iryek-rpi/pico-encoder/hw/case/case.jpg

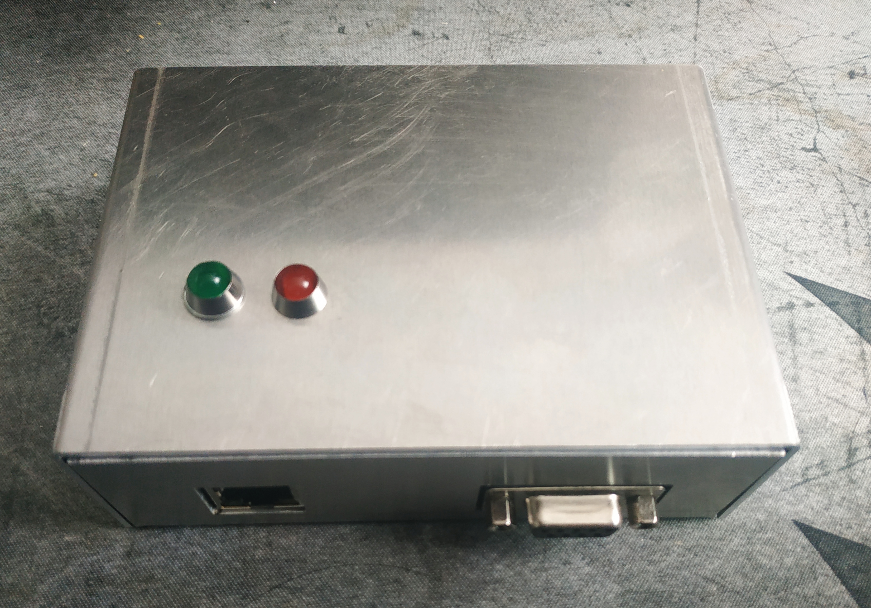
hw/case/case.jpg
