iryek-rpi/pico-encoder/hw/case/silk/chuja-si.jpg

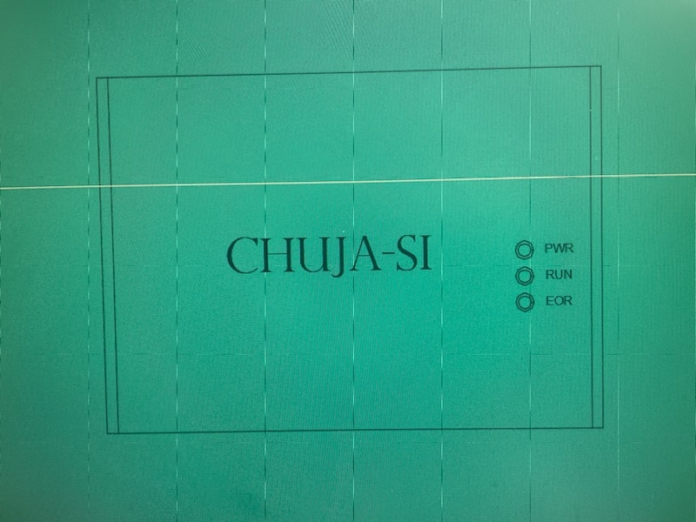
hw/case/silk/chuja-si.jpg
