iryek-rpi/pico-encoder/hw/case/silk/front-back.jpg

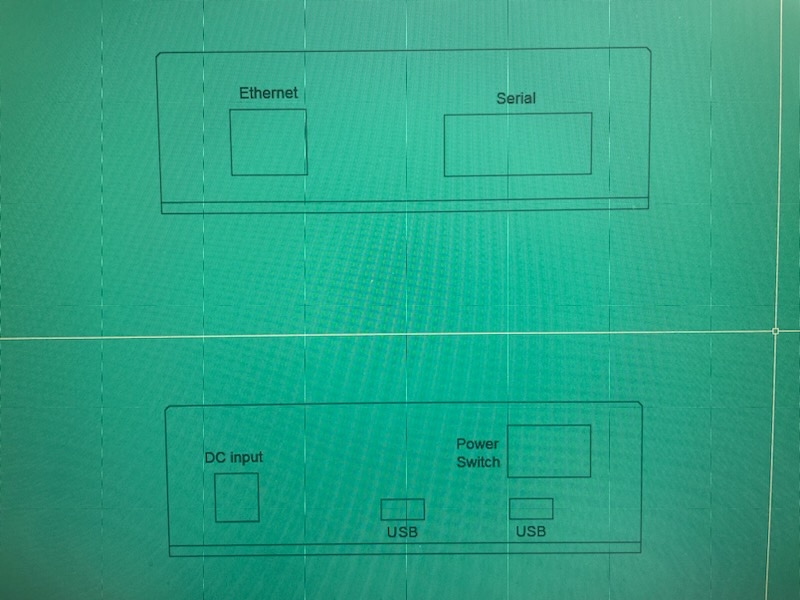
hw/case/silk/front-back.jpg
