iryek-rpi/pico-encoder/hw/share/connected0.png

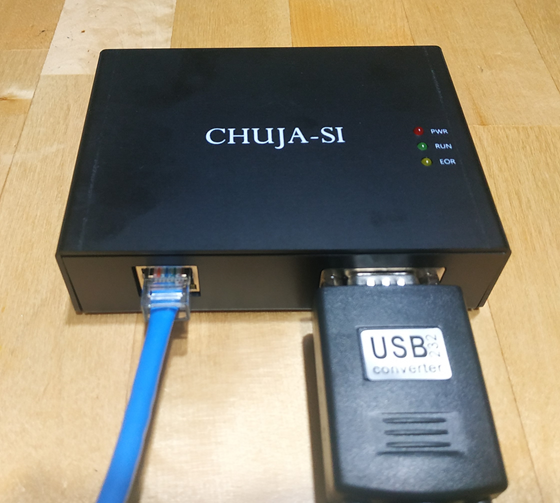
hw/share/connected0.png
