iryek-rpi/pico-encoder/kc/w5500-evb-pico-pcb.png

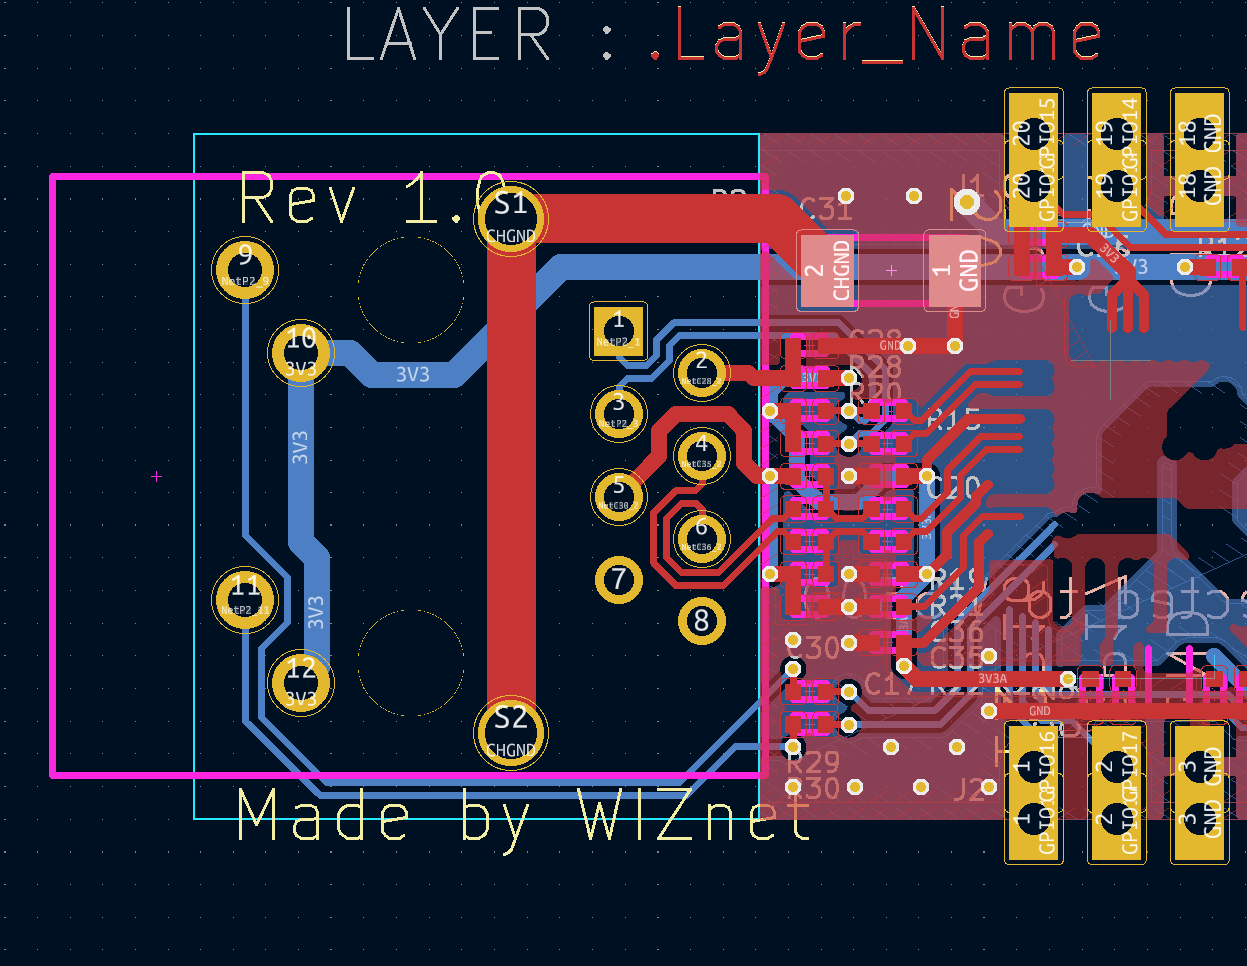
kc/w5500-evb-pico-pcb.png
