iryek-rpi/pico-encoder/kc/w5500-evb-pico-sch.png

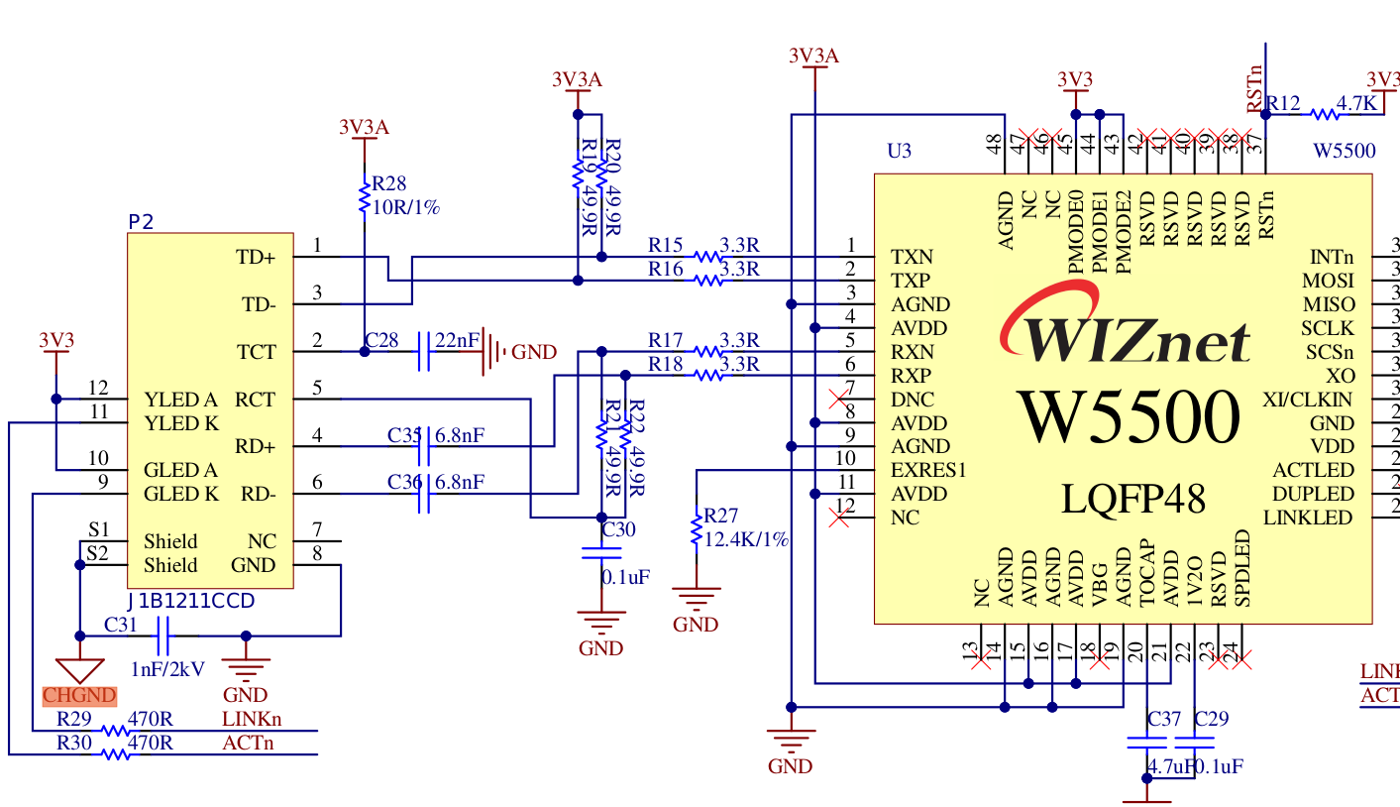
kc/w5500-evb-pico-sch.png
