iryek-rpi/pico-encoder/kc/w5500-rvb-pico-board.jpg

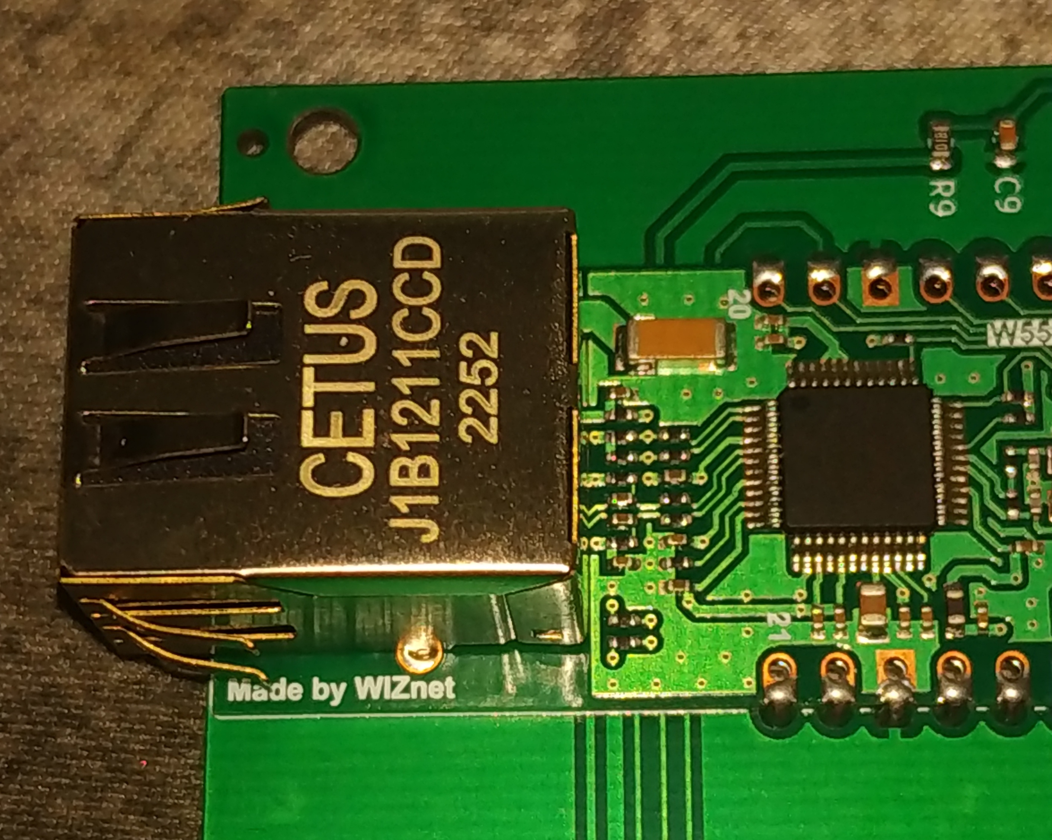
kc/w5500-rvb-pico-board.jpg
