iryek-rpi/pico-encoder/sw/ex/web/html/pyramid-1600.jpg

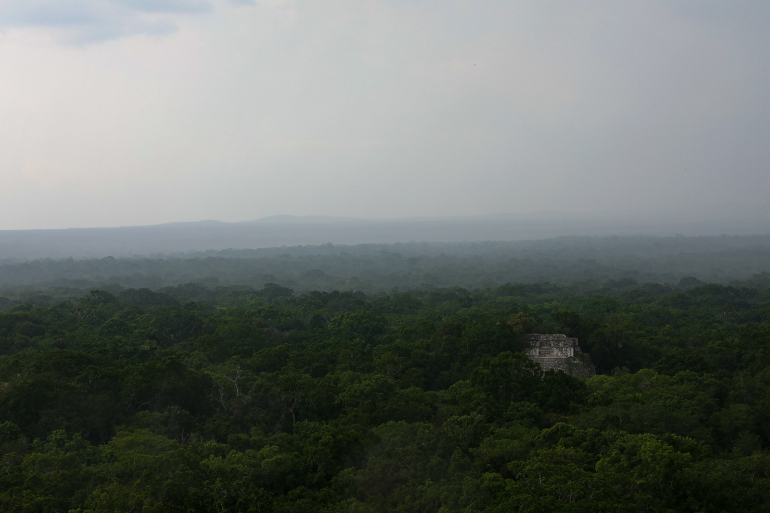
sw/ex/web/html/pyramid-1600.jpg
