iryek-rpi/pico-encoder/sw/release/w5500-2023.12.21/thonny_capture.png

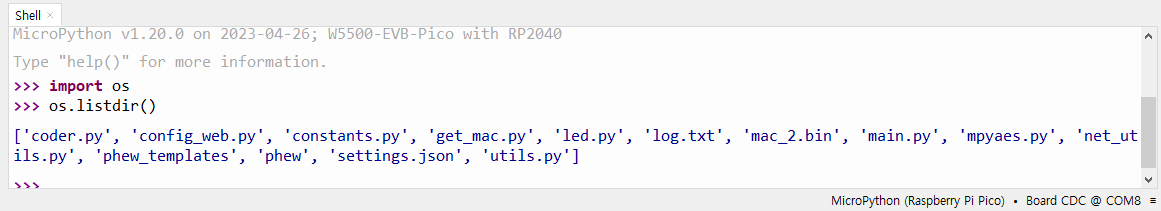
sw/release/w5500-2023.12.21/thonny_capture.png
