iryek-rpi/pico-encoder/hw/parts/Resistors/68K_0.125W_0805/1810161334_HKR-Hong-Kong-Resistors-RCT0568KFLF_C178222.pdf

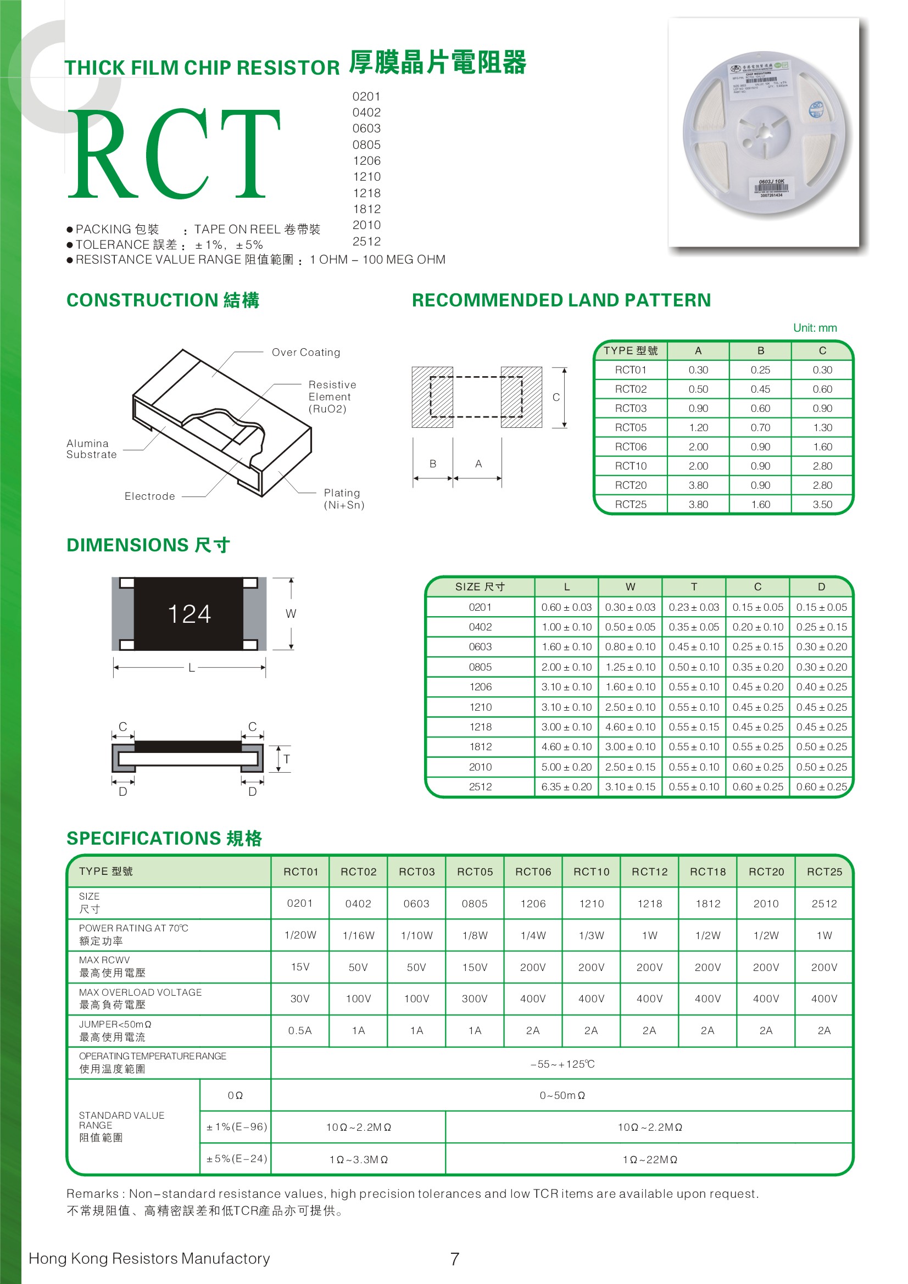
[picture p19: page 1]
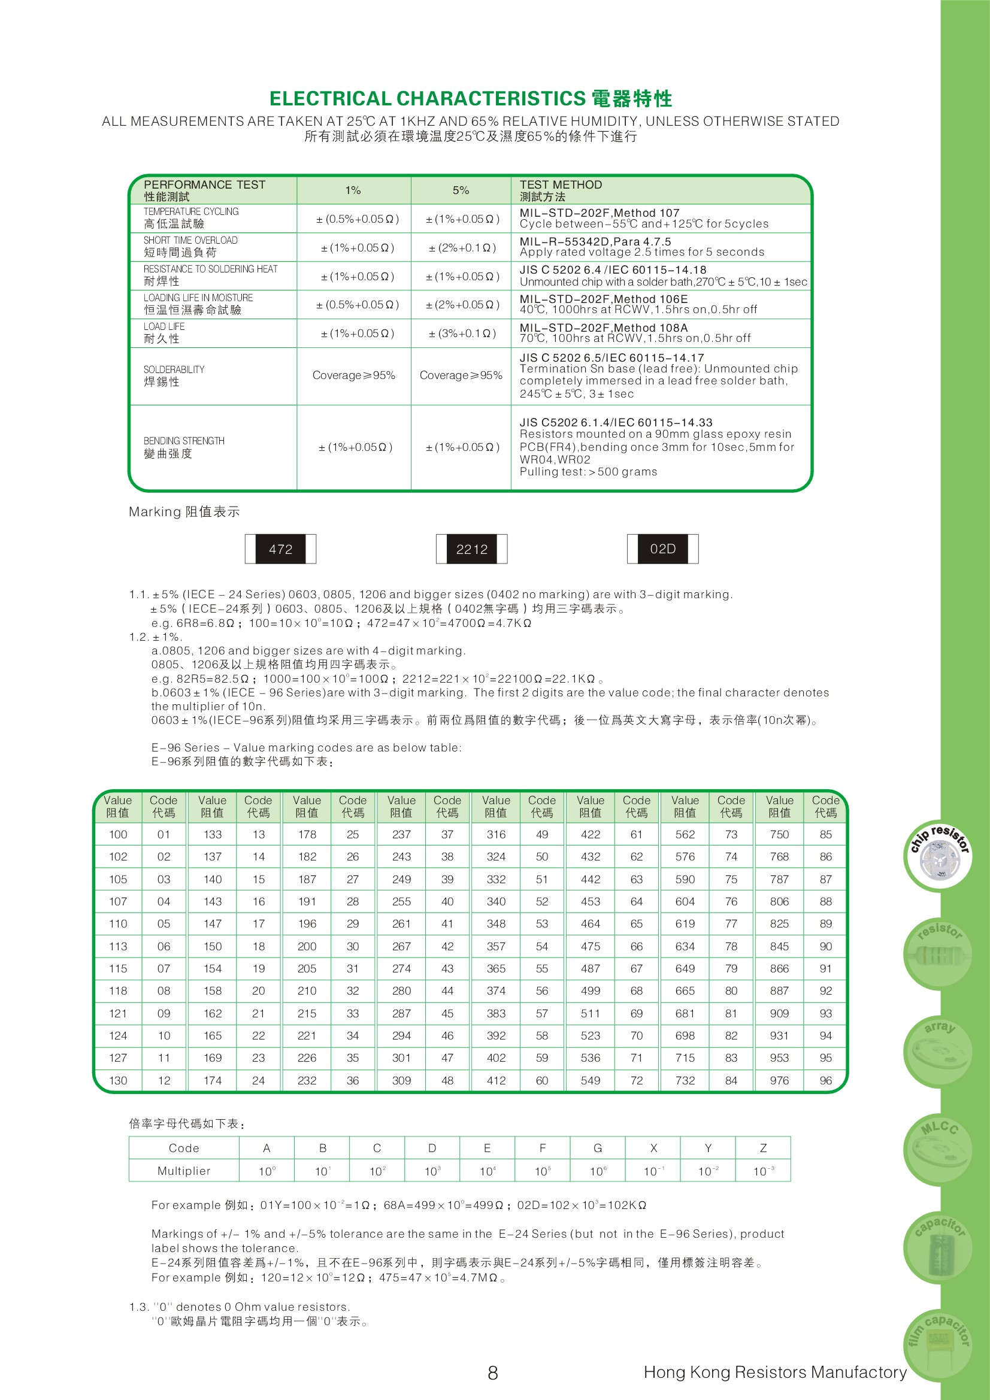
[picture p20: page 2]
