iryek-rpi/pico-encoder/hw/case/2023.5.26_order/2023.5.30_케이스_상하판/상판.png

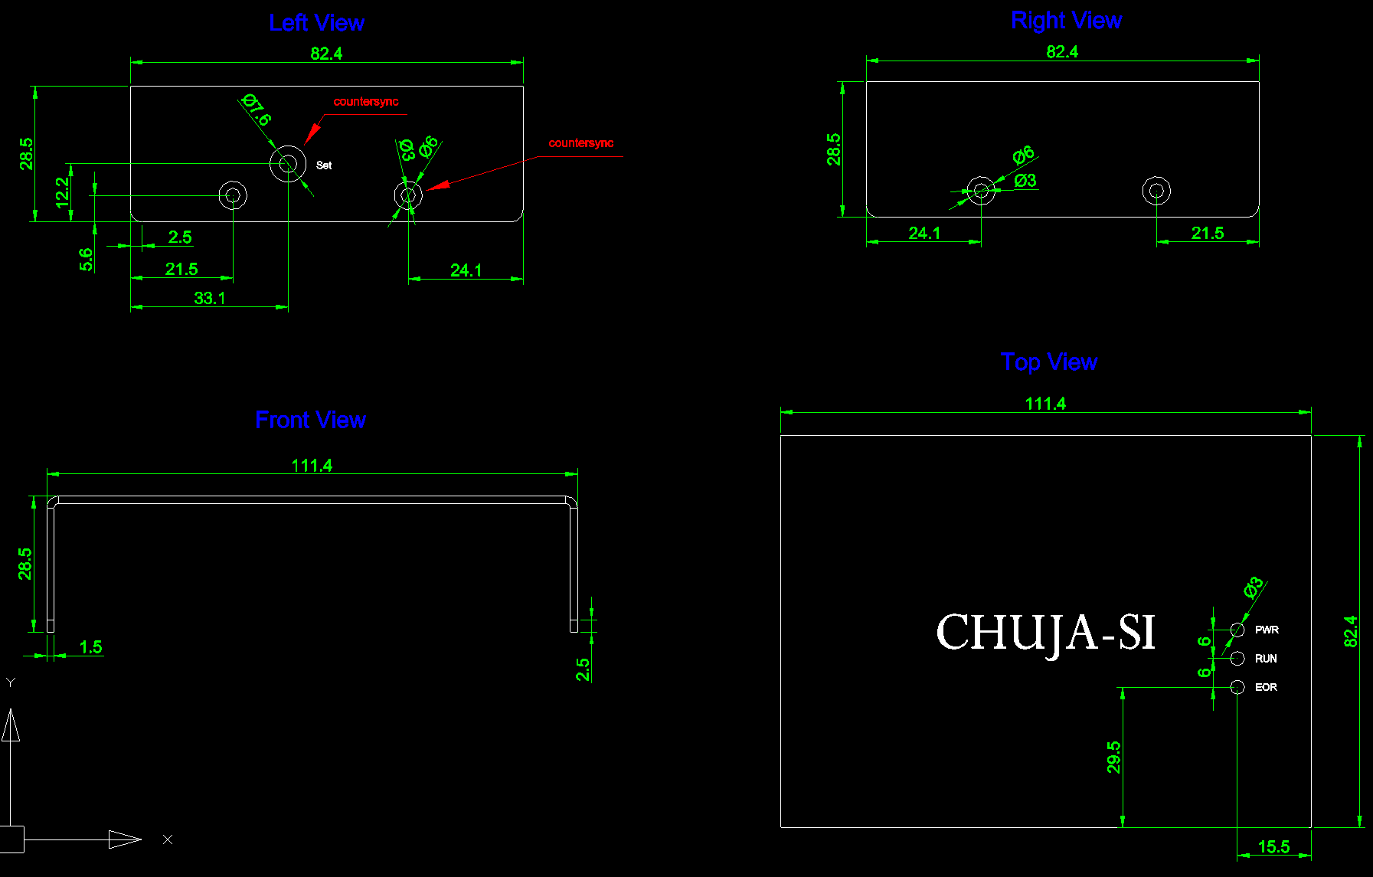
hw/case/2023.5.26_order/2023.5.30_케이스_상하판/상판.png
