iryek-rpi/pico-encoder/hw/case/2023.5.26_order/폰트캡춰.PNG

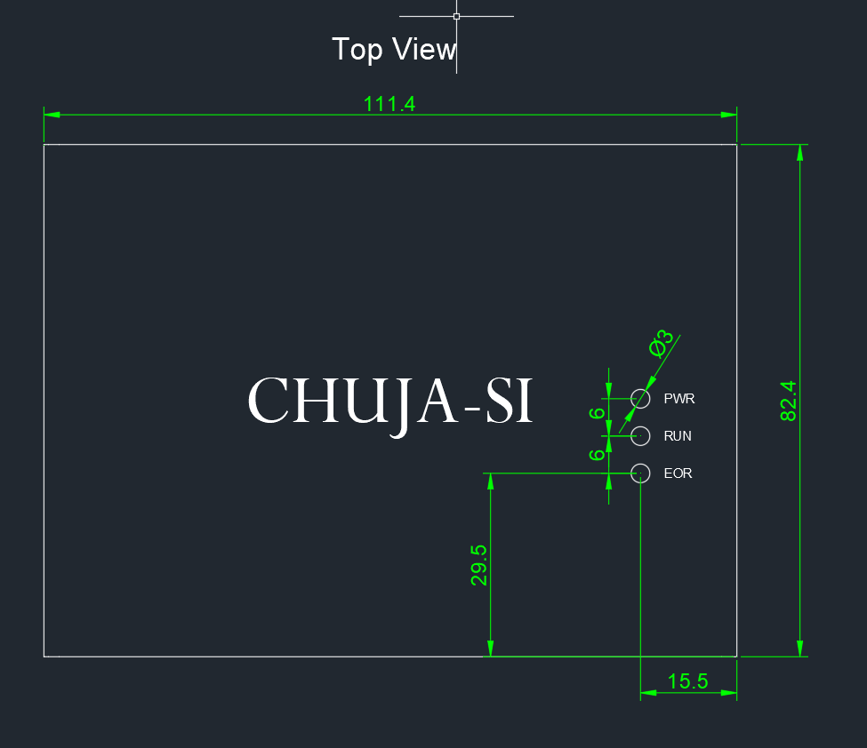
hw/case/2023.5.26_order/폰트캡춰.PNG
