iryek-rpi/pico-encoder/hw/parts/barrel-jack/dc_barrel_jack-5.5.png

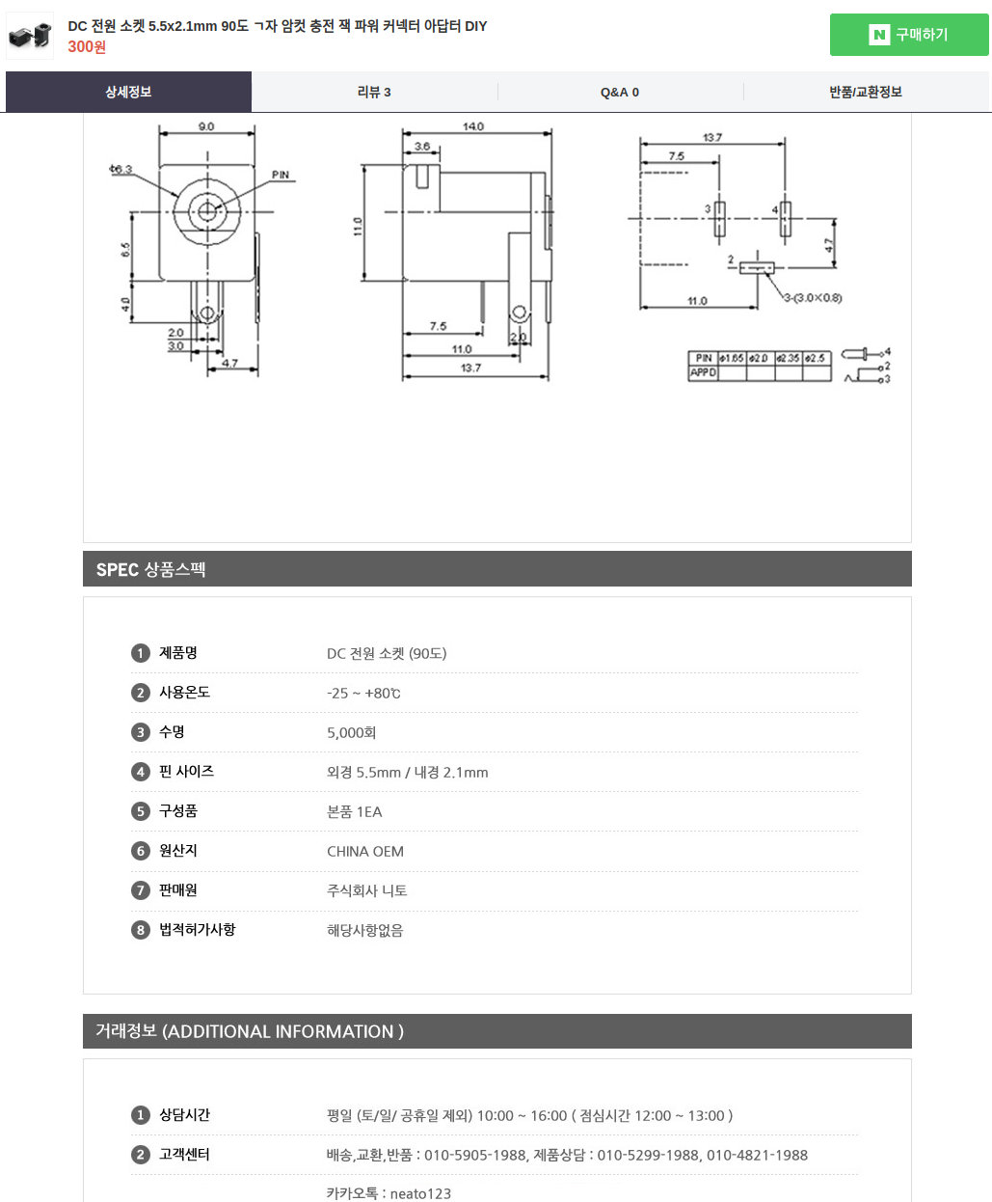
hw/parts/barrel-jack/dc_barrel_jack-5.5.png
