iryek-rpi/pico-encoder/hw/parts/Din-Rail-Bracket-DRB35-70-30/12544961_tmp_f172f1ada4b629af6b1564cea64bd3c32789view.jpg

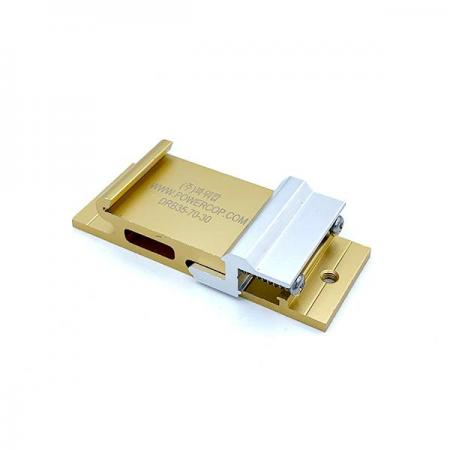
hw/parts/Din-Rail-Bracket-DRB35-70-30/12544961_tmp_f172f1ada4b629af6b1564cea64bd3c32789view.jpg
