iryek-rpi/pico-encoder/hw/parts/LED/LED_정전자1.png

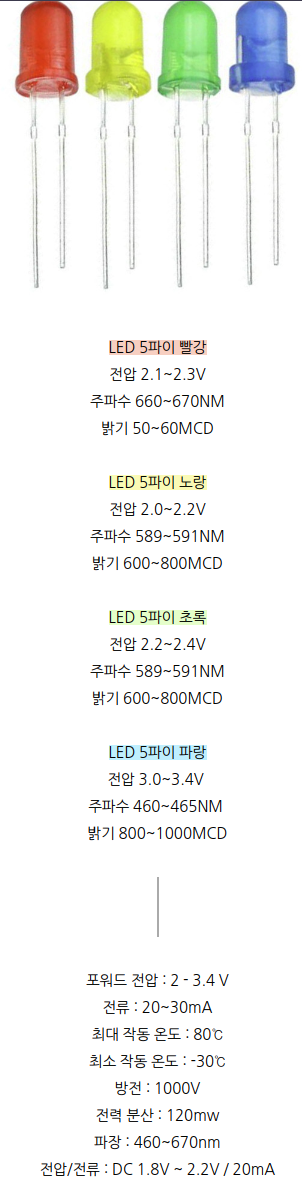
hw/parts/LED/LED_정전자1.png
