iryek-rpi/pico-encoder/hw/parts/LED/LED_정전자2.png

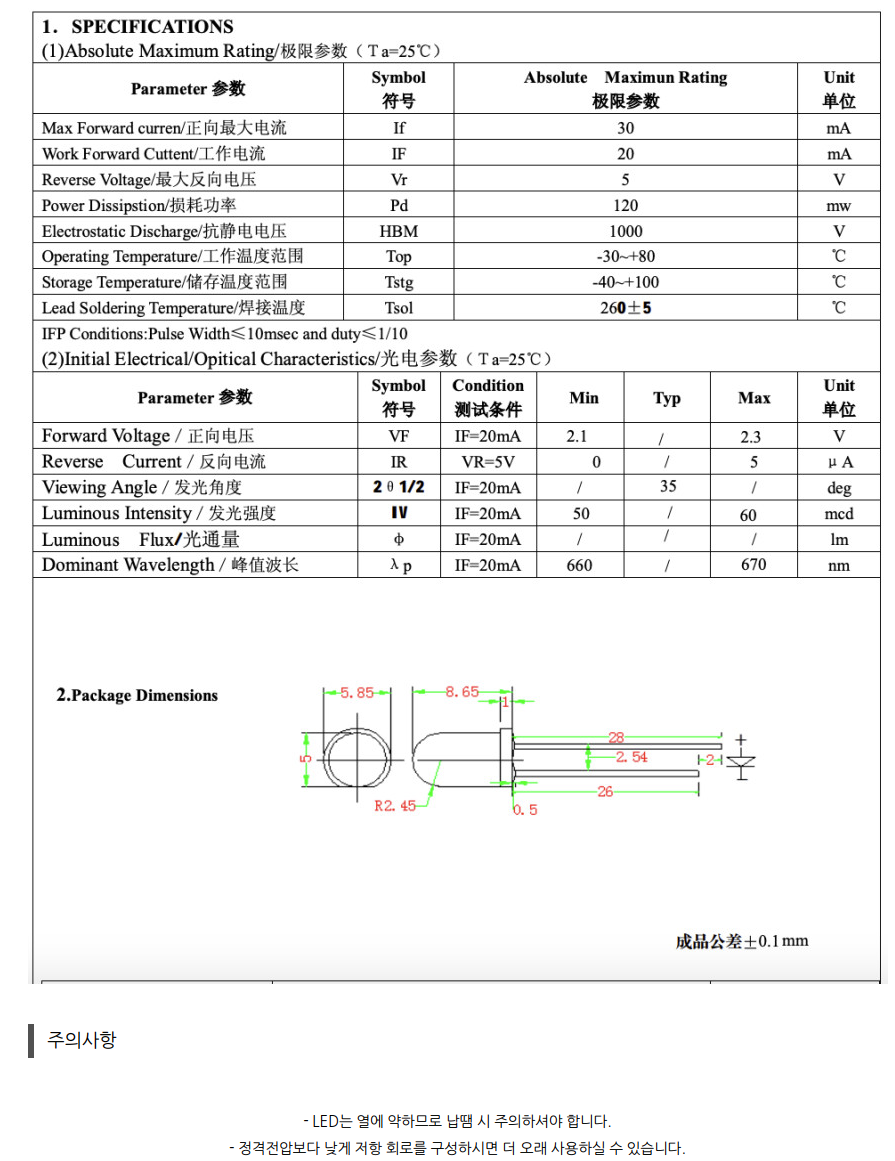
hw/parts/LED/LED_정전자2.png
