iryek-rpi/pico-encoder/hw/parts/molex/molex_5267-02_youtube.png

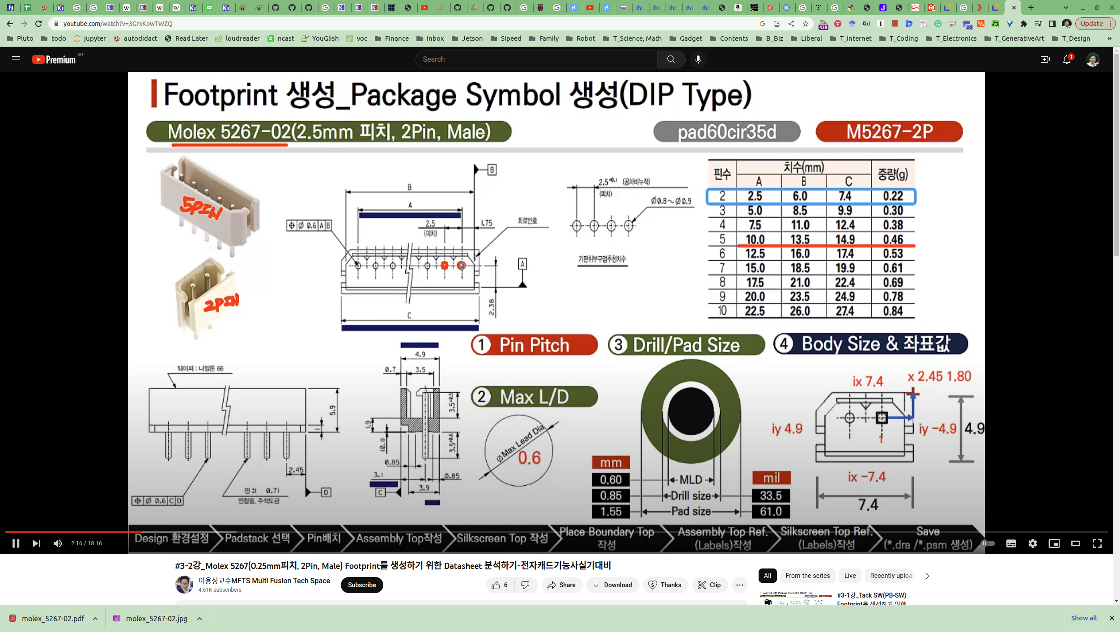
hw/parts/molex/molex_5267-02_youtube.png
