iryek-rpi/pico-encoder/hw/parts/MP1584EN_Switching-Regulator/MP1584_Fixed-5v/MP1584_5v_sch.png

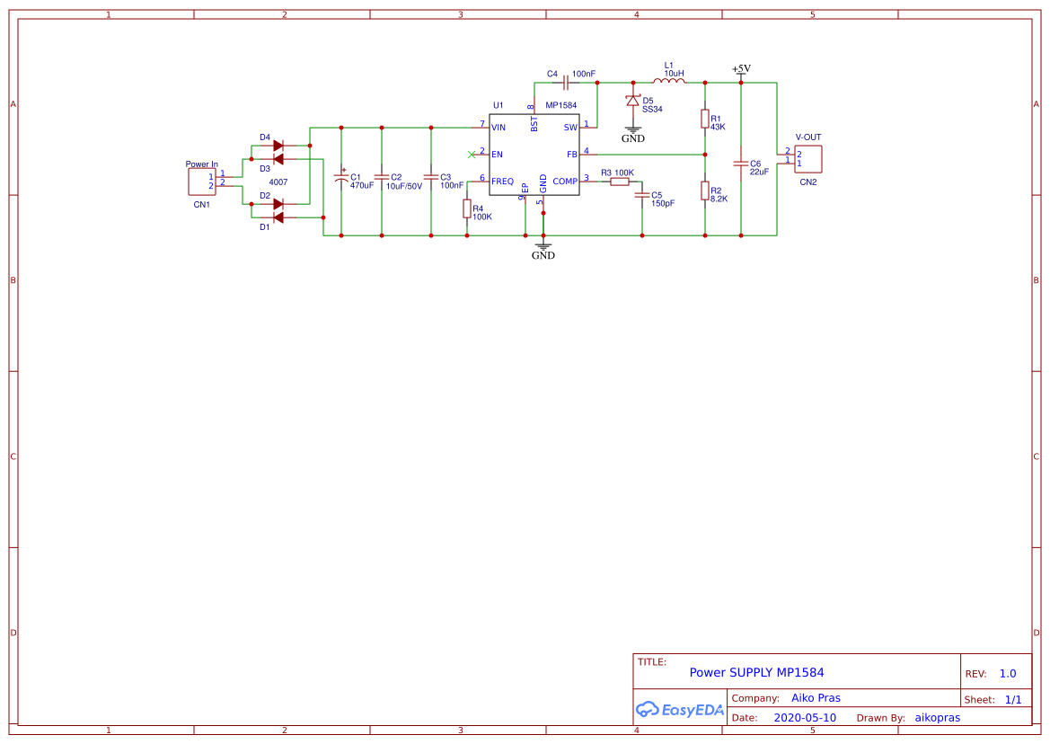
hw/parts/MP1584EN_Switching-Regulator/MP1584_Fixed-5v/MP1584_5v_sch.png
