iryek-rpi/pico-encoder/hw/case/case_base.stl

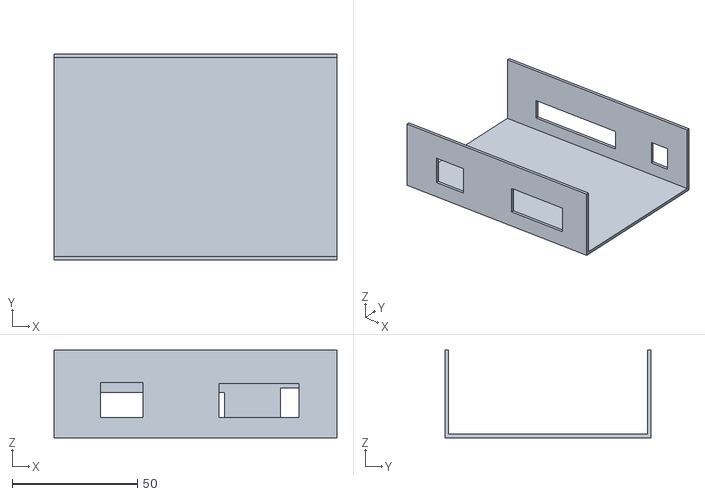
[picture p49: CAD file, 2023-04-25]
hw/case/case_base.stl
113.0 x 82.3 x 35.0
