iryek-rpi/pico-encoder/hw/parts/W5500-EVB-Pico/altium2kicad/W5500-EVB-Pico_V100-PcbDoc/Root Entry/Models/9.dat.step

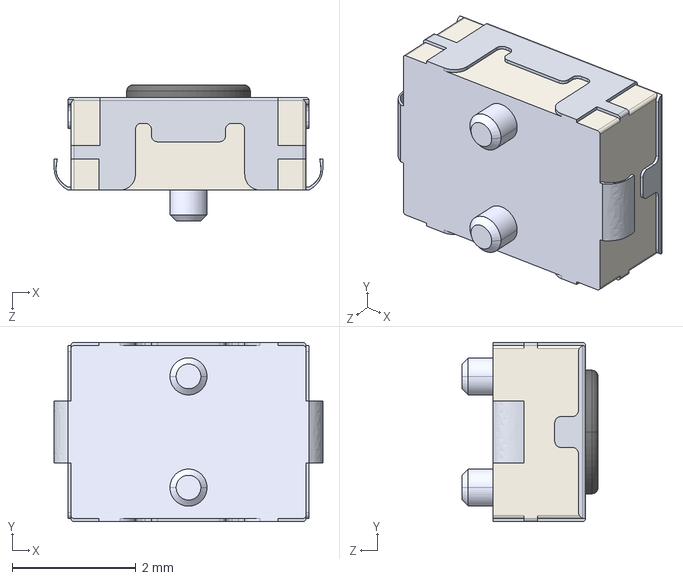
[picture p50: CAD file, 2023-03-22]
hw/parts/W5500-EVB-Pico/altium2kicad/W5500-EVB-Pico_V100-PcbDoc/Root Entry/Models/9.dat.step
4.35 x 2.90 x 2.20 mm
