iryek-rpi/pico-encoder/hw/case/case-v2/dxf/top_left_3d.dxf

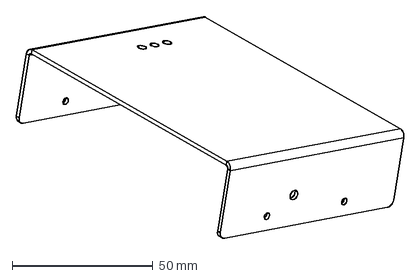
[picture p51: CAD file, 2023-05-24]
hw/case/case-v2/dxf/top_left_3d.dxf
137.6 x 78.7 mm
