iryek-rpi/pico-encoder/hw/parts/W5500-EVB-Pico/altium2kicad/W5500-EVB-Pico_V100-PcbDoc/Root Entry/Models/23.dat.step

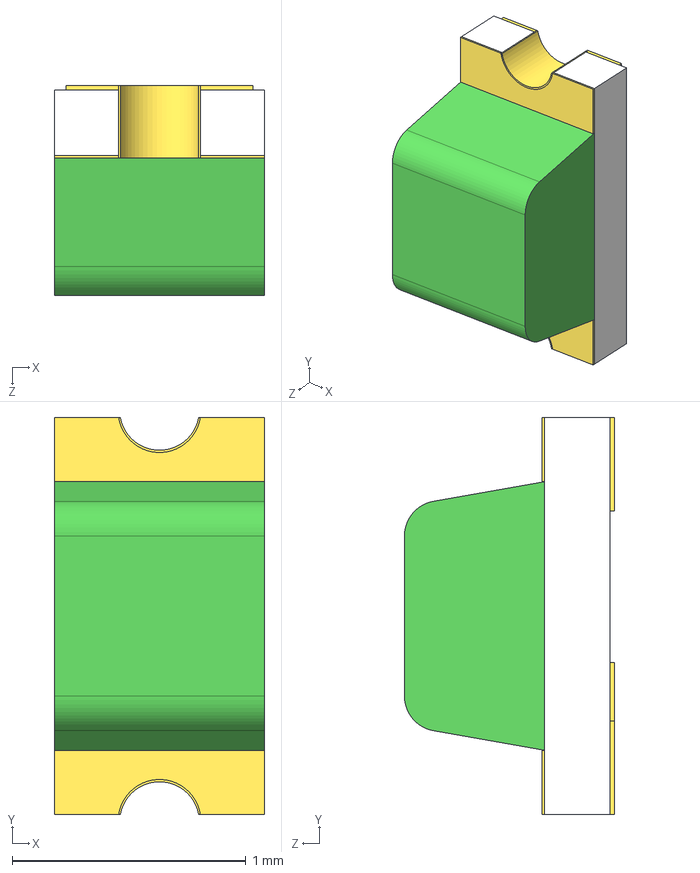
[picture p52: CAD file, 2023-03-22]
hw/parts/W5500-EVB-Pico/altium2kicad/W5500-EVB-Pico_V100-PcbDoc/Root Entry/Models/23.dat.step
0.9 x 1.70 x 0.9 mm
User Library-LTST-C190GKT_Pad005
User Library-LTST-C190GKT_Pad001
User Library-LTST-C190GKT_Pad004
User Library-LTST-C190GKT_Pad003
User Library-LTST-C190GKT_Lens
User Library-LTST-C190GKT_Pad
