iryek-rpi/pico-encoder/hw/parts/W5500-EVB-Pico/altium2kicad/W5500-EVB-Pico_V100-PcbDoc/Root Entry/Models/24.dat.step

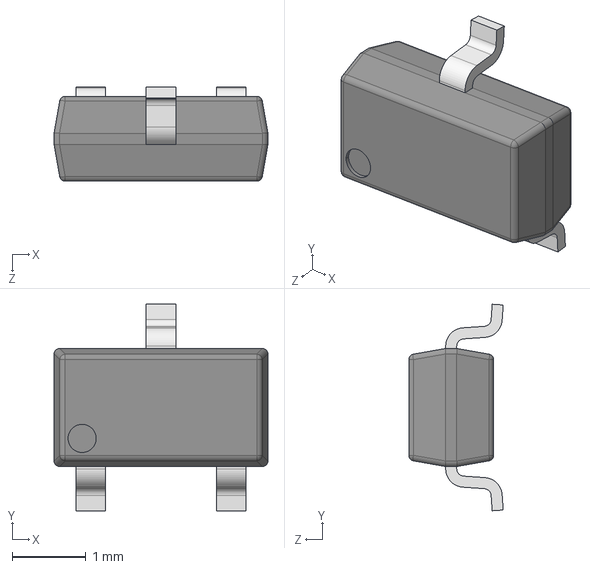
[picture p53: CAD file, 2023-03-22]
hw/parts/W5500-EVB-Pico/altium2kicad/W5500-EVB-Pico_V100-PcbDoc/Root Entry/Models/24.dat.step
2.90 x 2.80 x 1.28 mm
