iryek-rpi/pico-encoder/hw/parts/W5500-EVB-Pico/altium2kicad/W5500-EVB-Pico_V100-PcbDoc/Root Entry/Models/7.dat.step

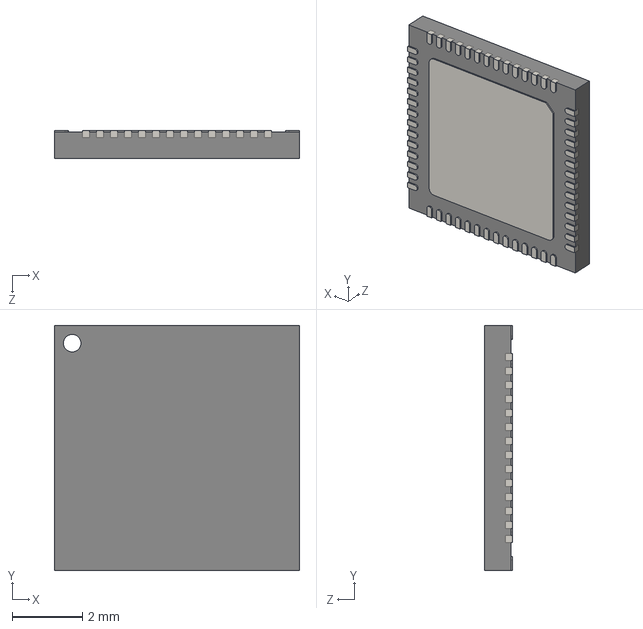
[picture p54: CAD file, 2023-03-22]
hw/parts/W5500-EVB-Pico/altium2kicad/W5500-EVB-Pico_V100-PcbDoc/Root Entry/Models/7.dat.step
7.00 x 7.00 x 0.8 mm
