iryek-rpi/pico-encoder/hw/case/case-v2/dxf/left.dxf

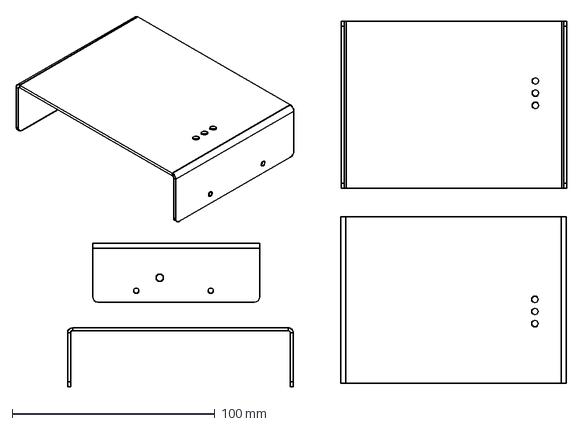
[picture p55: CAD file, 2023-05-24]
hw/case/case-v2/dxf/left.dxf
271.8 x 182.9 mm
