iryek-rpi/pico-encoder/hw/parts/W5500-EVB-Pico/altium2kicad/W5500-EVB-Pico_V100-PcbDoc/Root Entry/Models/6.dat.step

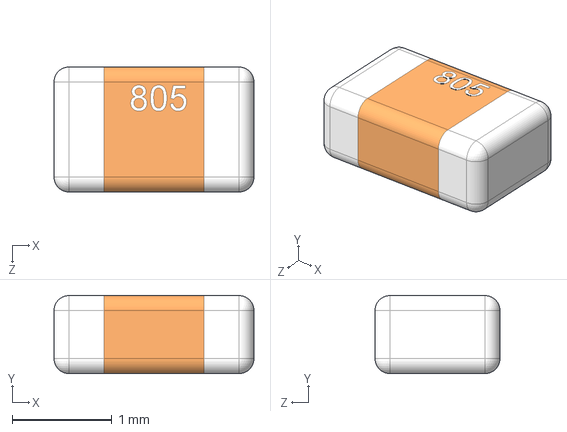
[picture p56: CAD file, 2023-03-22]
hw/parts/W5500-EVB-Pico/altium2kicad/W5500-EVB-Pico_V100-PcbDoc/Root Entry/Models/6.dat.step
2.00 x 0.782 x 1.25 mm
