iryek-rpi/pico-encoder/hw/case/case-v2/dxf/top_right_3d.dxf

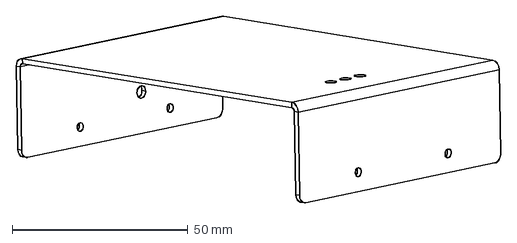
[picture p57: CAD file, 2023-05-24]
hw/case/case-v2/dxf/top_right_3d.dxf
137.8 x 53.1 mm
