iryek-rpi/pico-encoder/hw/case/case-v2/dxf/base.dxf

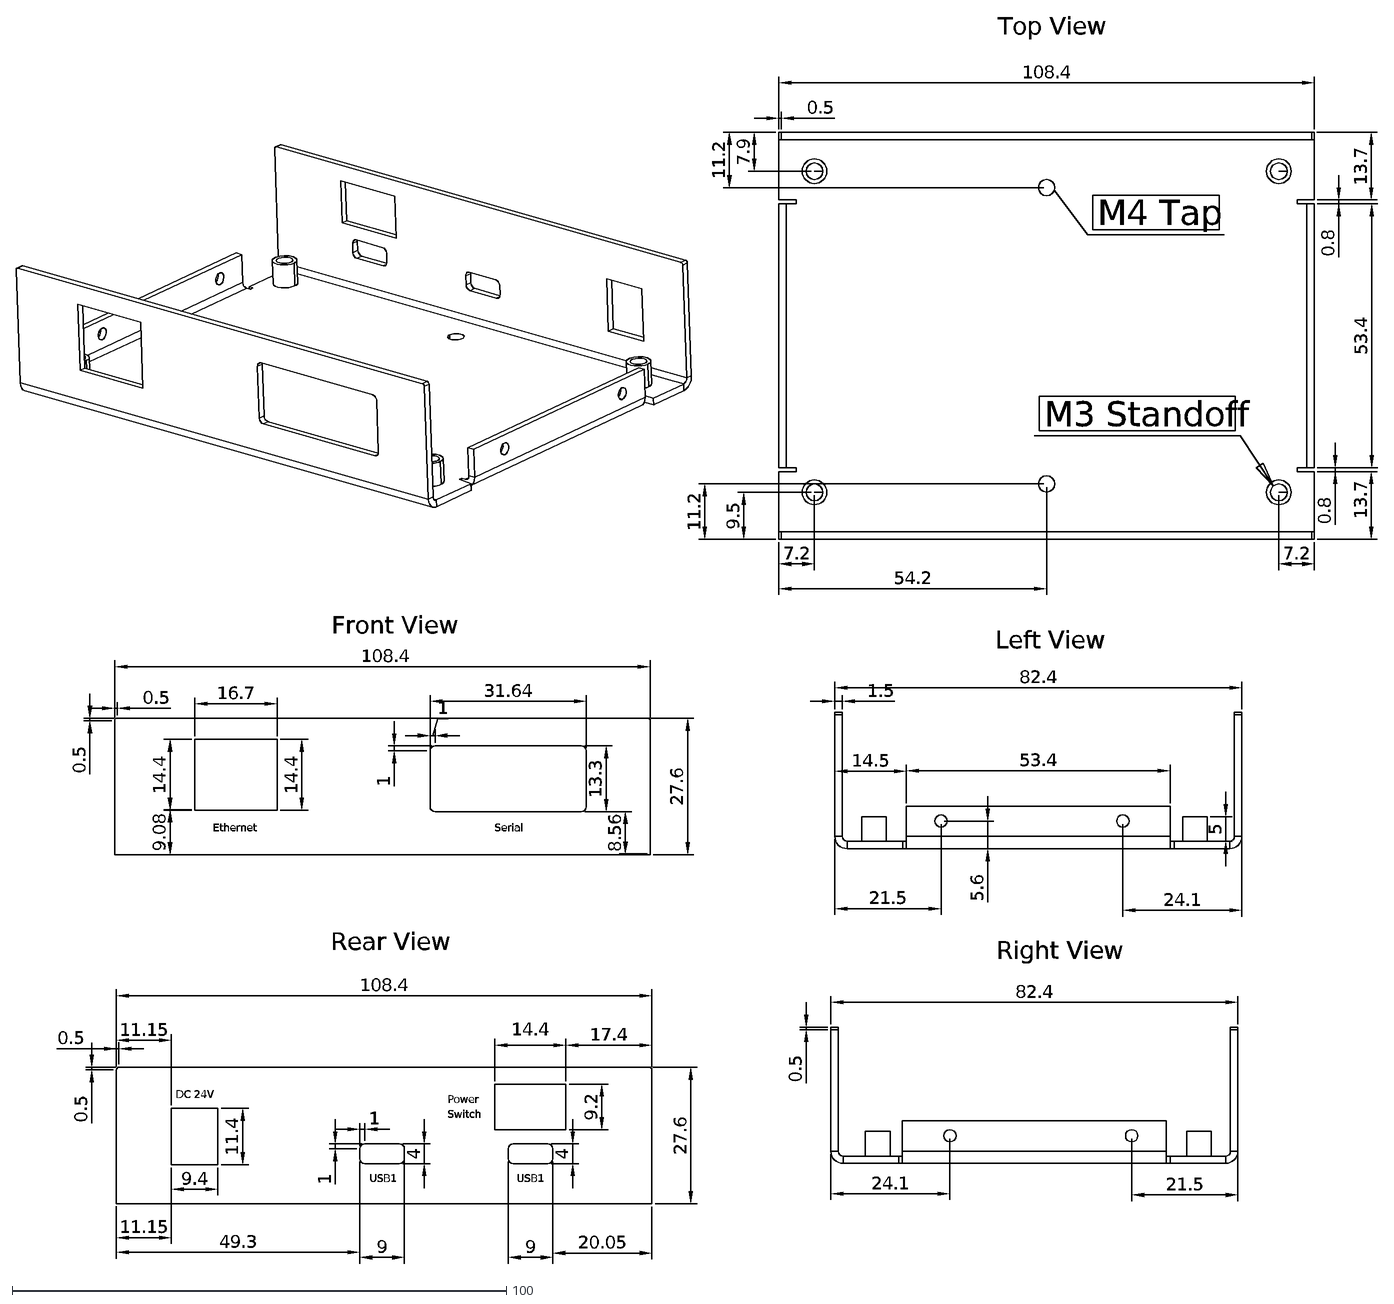
[picture p59: CAD file, 2023-05-24]
hw/case/case-v2/dxf/base.dxf
108.4
0.5
1
9.4
14.4
82.4
24.1
21.5
Left View
Right View
11.4
27.6
13.3
9.08
8.56
5
53.4
1.5
9.2
5.6
16.7
31.64
4
11.15
49.3
20.05
9
17.4
DC 24V
USB1
Power
Switch
Ethernet
Serial
Front View
Rear View
Top View
9.5
7.9
7.2
54.2
11.2
14.5
M4 Tap
M3 Standoff
13.7
0.8
