iryek-rpi/pico-encoder/hw/case/case-v2/dxf/right_view.dxf

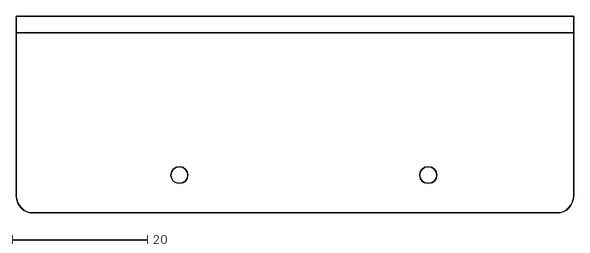
[picture p61: CAD file, 2023-05-14]
hw/case/case-v2/dxf/right_view.dxf
82.4 x 29.1
