iryek-rpi/pico-encoder/hw/parts/W5500-EVB-Pico/altium2kicad/W5500-EVB-Pico_V100-PcbDoc/Root Entry/Models/21.dat.step

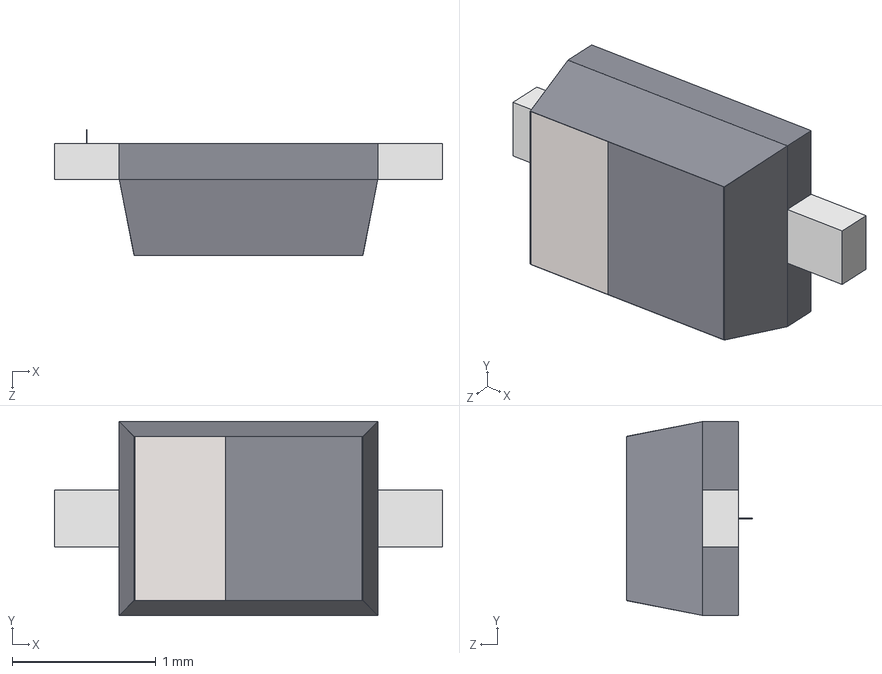
[picture p66: CAD file, 2023-03-22]
hw/parts/W5500-EVB-Pico/altium2kicad/W5500-EVB-Pico_V100-PcbDoc/Root Entry/Models/21.dat.step
2.70 x 1.35 x 0.875 mm
SW3dPS-SOD-323F_Board5
SW3dPS-SOD-323F_Extruded9 x 2
SW3dPS-SOD-323F_Board4 x 2
SW3dPS-SOD-323F_Extruded8 x 2
SW3dPS-SOD-323F_Extruded10 x 2
SW3dPS-SOD-323F_Board3 x 2
SW3dPS-SOD-323F_Extruded7
SW3dPS-SOD-323F_Extruded6
SW3dPS-SOD-323F_Extruded11
