iryek-rpi/pico-encoder/hw/parts/W5500-EVB-Pico/altium2kicad/W5500-EVB-Pico_V100-PcbDoc/Root Entry/Models/14.dat.step

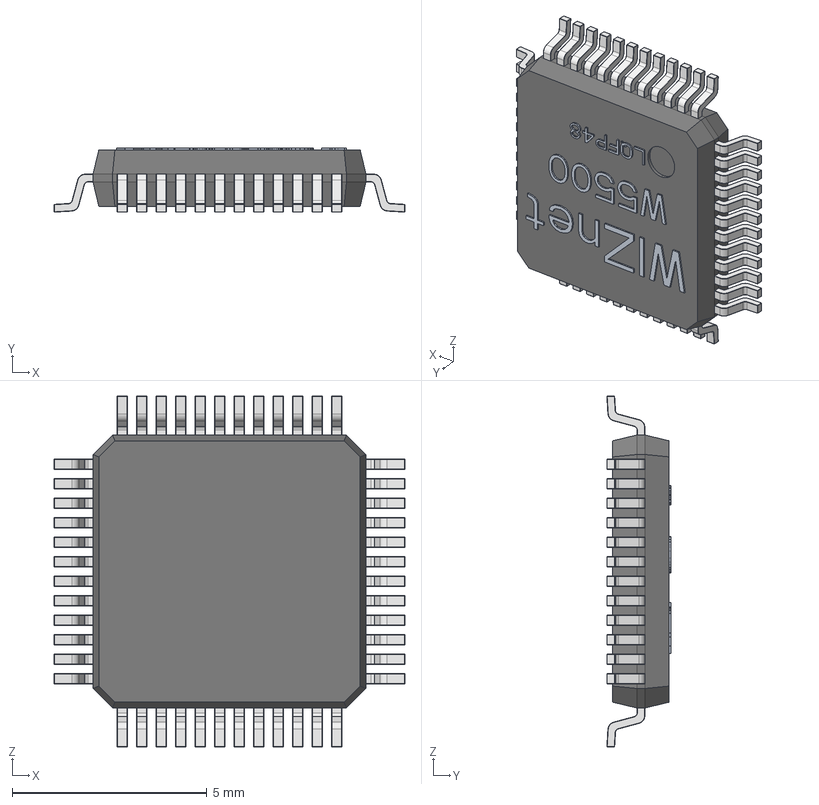
[picture p67: CAD file, 2023-03-22]
hw/parts/W5500-EVB-Pico/altium2kicad/W5500-EVB-Pico_V100-PcbDoc/Root Entry/Models/14.dat.step
9.00 x 1.65 x 9.00 mm
USER_LIBRARY-LQFP48_GRID_0-3644 x 48
USER_LIBRARY-LQFP48_GRID_0-1682
_LQFP48
