iryek-rpi/pico-encoder/epc_2023.10.19/kc/manual/app_with_msg_textbox.PNG

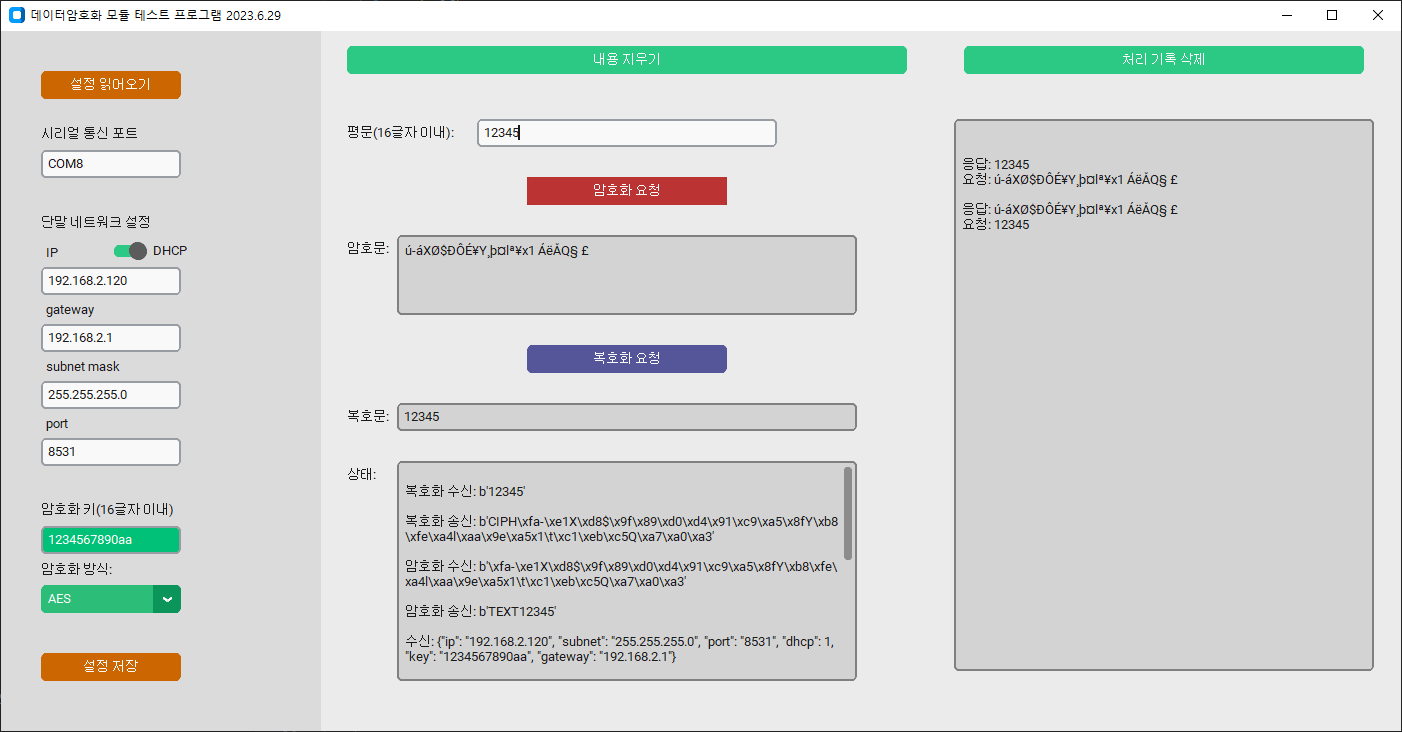
epc_2023.10.19/kc/manual/app_with_msg_textbox.PNG
