iryek-rpi/pico-encoder/hw/pcb_wired_v1/pdf/2023.6.5-sch.pdf/회로도.pdf

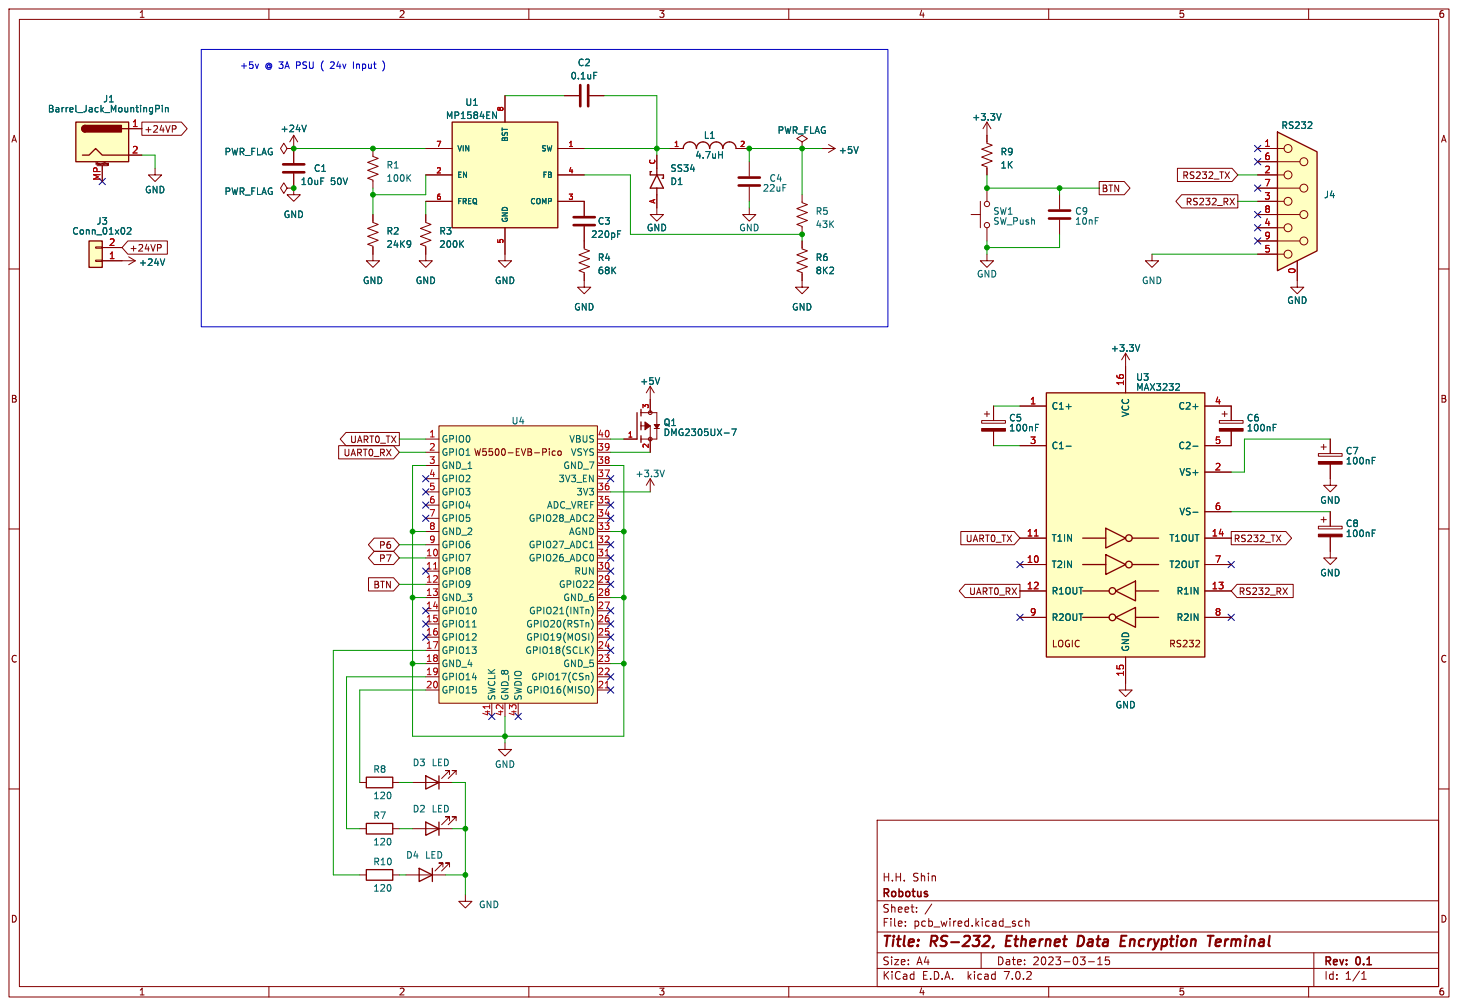
[picture p70: page 1]

A C GND GND GND GND
