iryek-rpi/pico-encoder/hw/pcb_v6/pdf/2023.5.18.sch.pdf/pcb.pdf

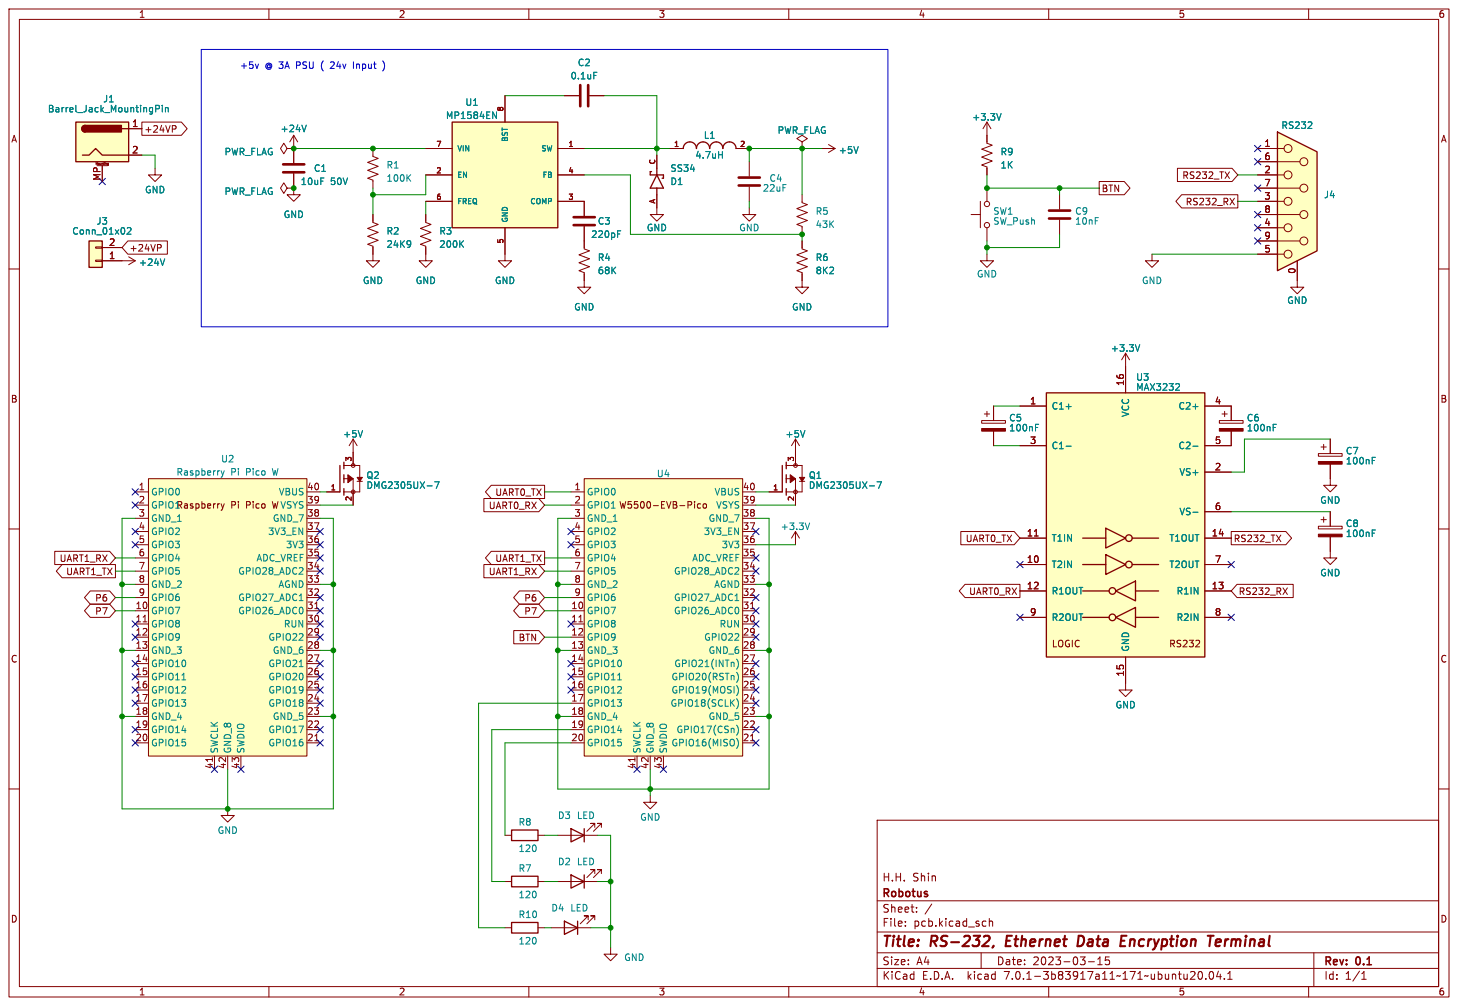
[picture p71: page 1]

3 2 Q1 DMG2305UX-7 W5500-EVB-Pico GPIO0 1 GPIO7 10 GPIO8 11 GPIO9 12 GND_3 13 GPIO10 14 GPIO11 15 GPIO12 16 GPIO13 17 GND_4 18 GPIO14 19 GPIO1 2 GPIO15 20 GPIO16(MISO) 21 GPIO17(CSn) 22 GND_5 23 GPIO18(SCLK) 24 GPIO19(MOSI) 25 GPIO20(RSTn) 26 GPIO21(INTn) 27 GND_6 28 GPIO22 29 GND_1 3 RUN 30 GPIO26_ADC0 31 GPIO27_ADC1 32 AGND 33 GPIO28_ADC2 34 ADC_VREF 35
