iryek-rpi/pico-encoder/hw/pcb_v6/pdf/2023.5.15_sch.pdf

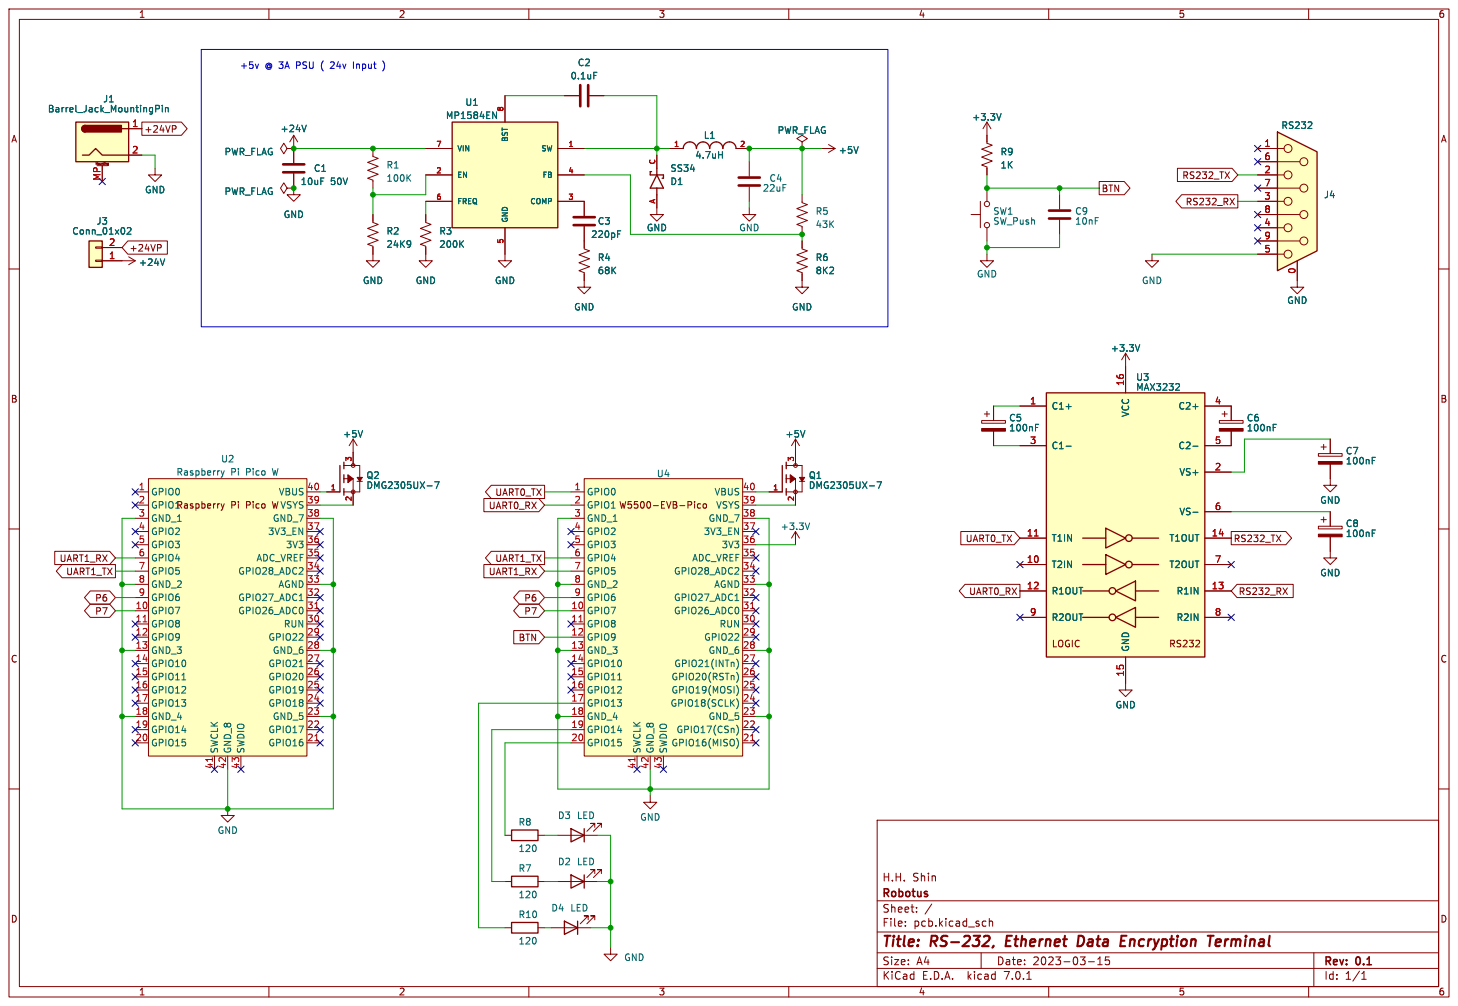
[picture p77: page 1]
