iryek-rpi/pico-encoder/hw/pcb_v6/pdf/2023.4.7.pcb.pdf

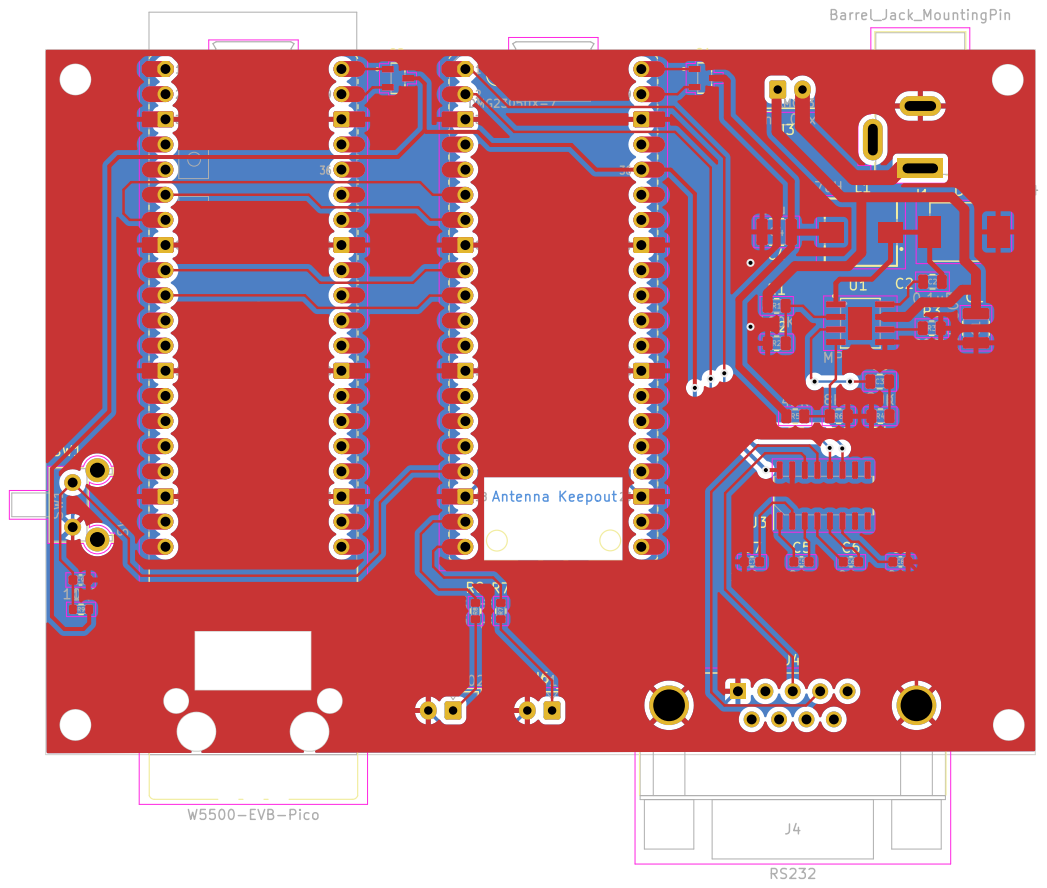
[picture p78: page 1]
