iryek-rpi/pico-encoder/hw/pcb_v6/pdf/2023.4.7.sch.pdf

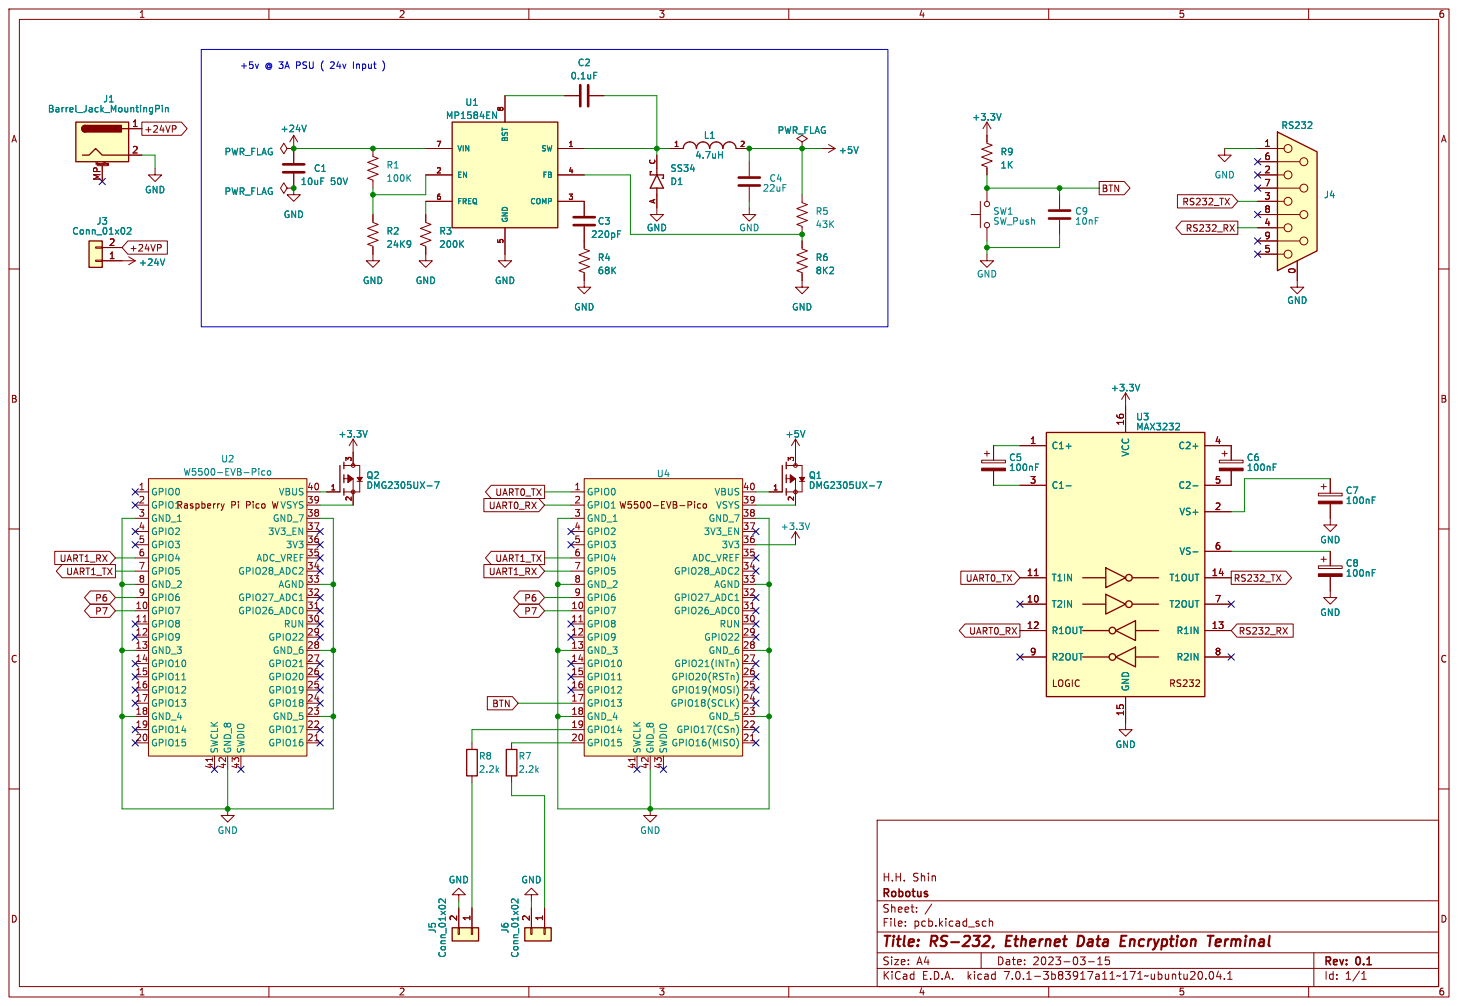
[picture p79: page 1]
