iryek-rpi/pico-encoder/hw/pcb_v6/pdf/2023.4.4.gerber.pdf/pcb-B_Mask.pdf

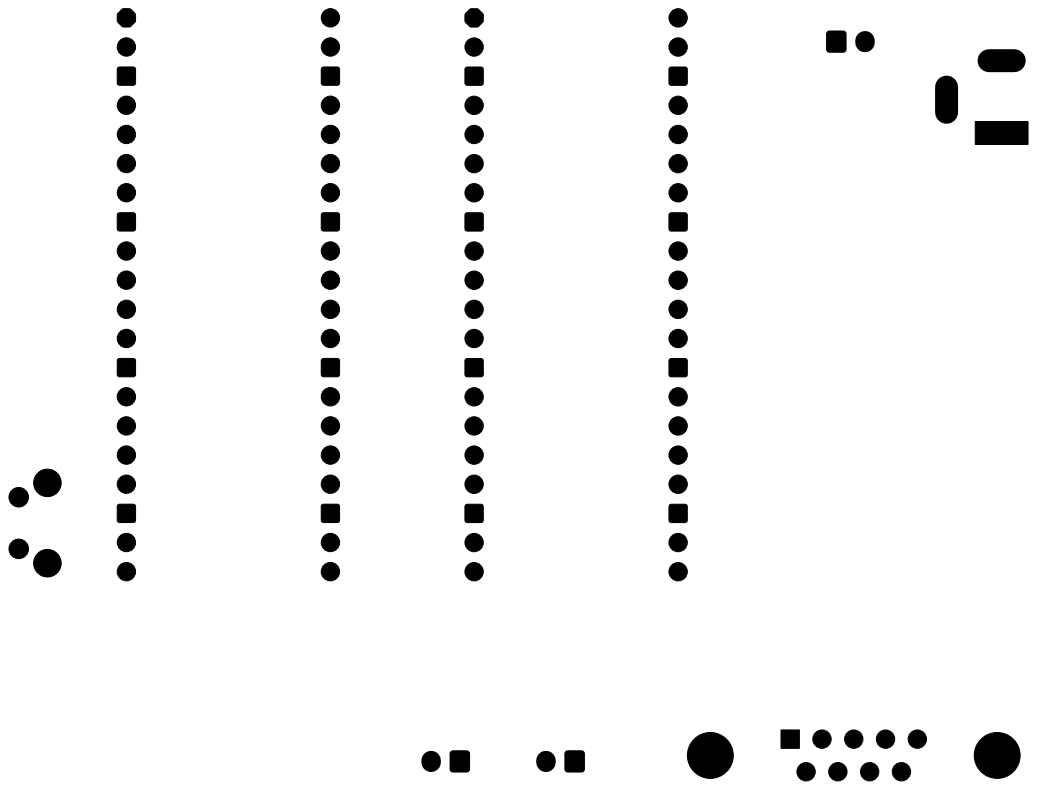
[picture p81: page 1]
