iryek-rpi/pico-encoder/hw/pcb_v6/pdf/2023.4.4.gerber.pdf/pcb-Edge_Cuts.pdf

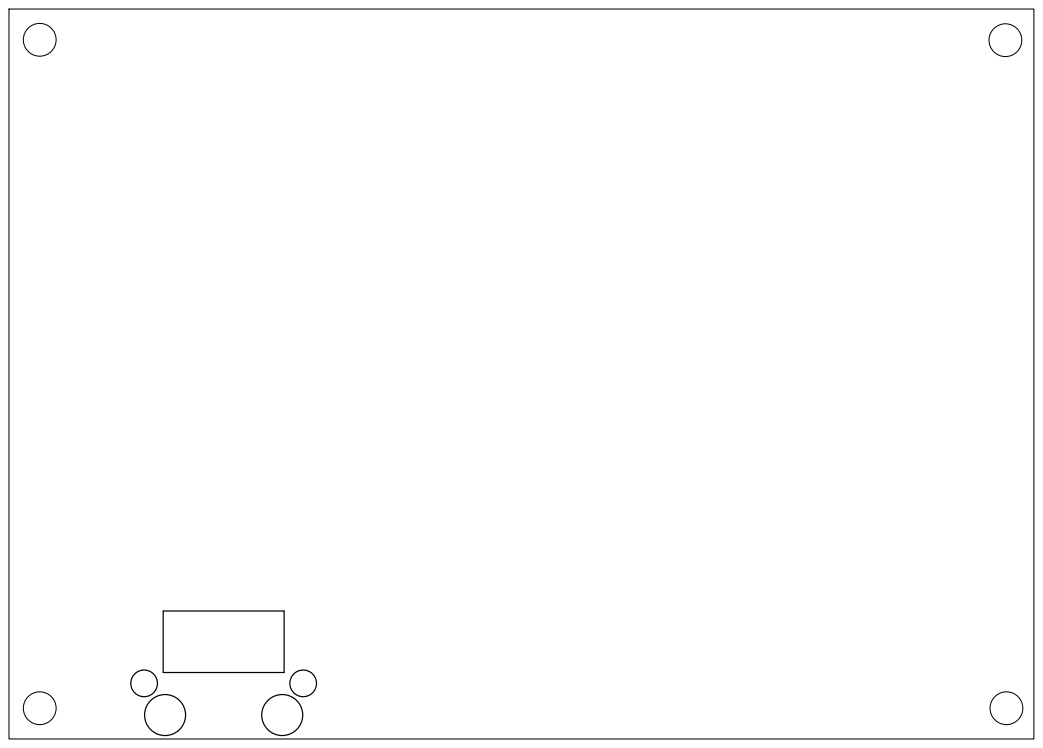
[picture p82: page 1]
