iryek-rpi/pico-encoder/hw/pcb_v6/pdf/2023.4.4.gerber.pdf/pcb-F_Paste.pdf

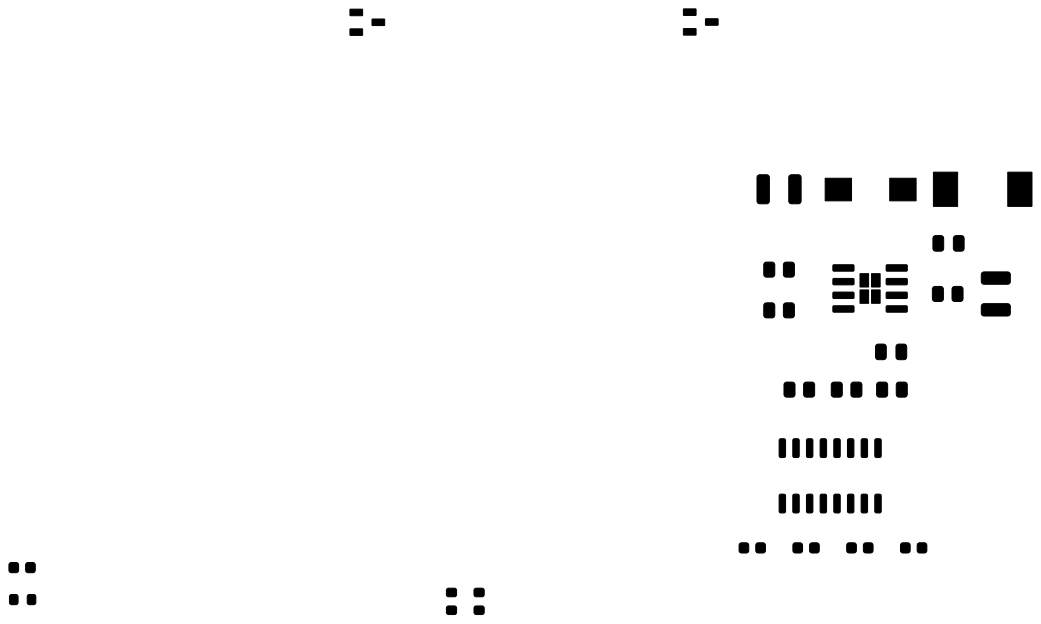
[picture p85: page 1]
