iryek-rpi/pico-encoder/sw/w5500/xor.py

import sys

def create_token(string):
    ascii_sum = sum(ord(char) for char in string) # 문자열의 각 문자의 ASCII 값을 더함
    token = ascii_sum % 256 # 1바이트 값으로 변환 (0-255 사이 값)
    return token

def xor_with_token(string, token):
    xor_result = [ord(char) ^ token for char in string] # 각 문자를 토큰 값으로 XOR 연산 수행
    return bytes(xor_result)

def xor_bin_with_token(bstr, token):
    #xor_result = [ord(char) ^ token for char in string] # 각 문자를 토큰 값으로 XOR 연산 수행
    xor_result = [b ^ token for b in bstr] # 각 문자를 토큰 값으로 XOR 연산 수행
    return bytes(xor_result)

def ascii_to_string(ascii_list):
    return ''.join(chr(val) for val in ascii_list) # ASCII 값 리스트를 문자열로 변환

if __name__ == '__main__':
    password = "password"  # 패스워드를 이용해 토큰 생성
    token = create_token(password)

    print(f'{"#"*10} original {"#"*10}')
    original_string ="This is a my data"  # 첫 번째 XOR 연산(encode)
    xor_result = xor_with_token(original_string, token)
    xor_result_str = ascii_to_string(xor_result)
    restored_result = xor_with_token(xor_result_str, token) # 두 번째 XOR 연산 (decode)
    restored_string = ascii_to_string(restored_result)

    print(f"Original string: '{original_string}'")
    print(f"Token: {token}")
    print(f"XOR result (ASCII values): {xor_result}")
    print(f"XOR result (as string): '{xor_result_str}'")
    print(f"Restored string: '{restored_string}'") 

    print(f'{"#"*10} Binary {"#"*10}')
    msg_bin = bytes(original_string, 'utf-8')
    xor_result_bin = xor_with_token(msg_bin, token)
    xor_result_bin_str = ascii_to_string(xor_result_bin)

    restored_result = xor_with_token(xor_result_bin_str, token) # 두 번째 XOR 연산 (decode)
    restored_string = ascii_to_string(restored_result)
    print(f"Restored string: '{restored_string}'") 
