iryek-rpi/pico-encoder/sw/ex/async/uart_async.py

# https://github.com/peterhinch/micropython-async/blob/master/v3/as_demos/auart_hd.py

# auart_hd.py
# Author: Peter Hinch
# Copyright Peter Hinch 2018-2020 Released under the MIT license

# Demo of running a half-duplex protocol to a device. The device never sends
# unsolicited messages. An example is a communications device which responds
# to AT commands.
# The master sends a message to the device, which may respond with one or more
# lines of data. The master assumes that the device has sent all its data when
# a timeout has elapsed.

# In this test a physical device is emulated by the Device class
# To test link X1-X4 and X2-X3

from machine import UART
import uasyncio as asyncio
#from primitives.delay_ms import Delay_ms

# Dummy device waits for any incoming line and responds with 4 lines at 1 second
# intervals.
class Device():
    def __init__(self, uart_no = 4):
        self.uart = UART(uart_no, 9600)
        self.swriter = asyncio.StreamWriter(self.uart, {})
        self.sreader = asyncio.StreamReader(self.uart)
        asyncio.create_task(self._run())

    async def _run(self):
        responses = ['Line 1', 'Line 2', 'Line 3', 'Goodbye']
        while True:
            res = await self.sreader.readline()
            for response in responses:
                await self.swriter.awrite("{}\r\n".format(response))
                # Demo the fact that the master tolerates slow response.
                await asyncio.sleep_ms(300)

# The master's send_command() method sends a command and waits for a number of
# lines from the device. The end of the process is signified by a timeout, when
# a list of lines is returned. This allows line-by-line processing.
# A special test mode demonstrates the behaviour with a non-responding device. If
# None is passed, no commend is sent. The master waits for a response which never
# arrives and returns an empty list.
class Master():
    def __init__(self, uart_no = 2, timeout=4000):
        self.uart = UART(uart_no, 9600)
        self.timeout = timeout
        self.swriter = asyncio.StreamWriter(self.uart, {})
        self.sreader = asyncio.StreamReader(self.uart)
        self.delay = Delay_ms()
        self.response = []
        asyncio.create_task(self._recv())

    async def _recv(self):
        while True:
            res = await self.sreader.readline()
            self.response.append(res)  # Append to list of lines
            self.delay.trigger(self.timeout)  # Got something, retrigger timer

    async def send_command(self, command):
        self.response = []  # Discard any pending messages
        if command is None:
            print('Timeout test.')
        else:
            await self.swriter.awrite("{}\r\n".format(command))
            print('Command sent:', command)
        self.delay.trigger(self.timeout)  # Re-initialise timer
        while self.delay.running():
            await asyncio.sleep(1)  # Wait for 4s after last msg received
        return self.response

async def main():
    print('This test takes 10s to complete.')
    master = Master()
    device = Device()
    for cmd in ['Run', None]:
        print()
        res = await master.send_command(cmd)
        # can use b''.join(res) if a single string is required.
        if res:
            print('Result is:')
            for line in res:
                print(line.decode('UTF8'), end='')
        else:
            print('Timed out waiting for result.')

def printexp():
    st = '''Expected output:
This test takes 10s to complete.

Command sent: Run
Result is:
Line 1
Line 2
Line 3
Goodbye

Timeout test.
Timed out waiting for result.
'''
    print('\x1b[32m')
    print(st)
    print('\x1b[39m')

def test():
    printexp()
    try:
        asyncio.run(main())
    except KeyboardInterrupt:
        print('Interrupted')
    finally:
        asyncio.new_event_loop()
        print('as_demos.auart_hd.test() to run again.')

test()
