iryek-rpi/pico-encoder/sw/ex/async/echo_server.py

# PyMOTW-3 example for asyncio
# https://pymotw.com/3/asyncio/io_coroutine.html

import asyncio
import logging
import sys

SERVER_ADDRESS = ('localhost', 10000)
logging.basicConfig(
    level=logging.DEBUG,
    format='%(name)s: %(message)s',
    stream=sys.stderr,
)
log = logging.getLogger('main')

async def echo(reader, writer):
    address = writer.get_extra_info('peername')
    log = logging.getLogger('echo_{}_{}'.format(*address))
    log.debug('connection accepted')

    while True:
        data = await reader.read(128)

        if data:
            log.debug('received {!r}'.format(data))
            writer.write(data)
            await writer.drain()
            log.debug('sent {!r}'.format(data))
        else:
            log.debug('closing')
            writer.close()
            return

event_loop = asyncio.get_event_loop()

# Create the server and let the loop finish the coroutine before
# starting the real event loop.
factory = asyncio.start_server(echo, *SERVER_ADDRESS)
server = event_loop.run_until_complete(factory)
log.debug('starting up on {} port {}'.format(*SERVER_ADDRESS))
